dubnubdubnub/Giris/hw/TMR2615F_osu_pad/ground_audit_report.md

# Ground audit: TMR2615F_osu_pad

Generated by ground_audit.py. All coordinates in mm.

## Key footprint positions

- **NT1** (NetTie_2): (116.95, 99.40)
- **U7** (AT32F405RBT7-7): (99.00, 107.50)
- **U13** (TMR2615x): (110.00, 121.00)
- Distance NT1 -> U7: 19.69 mm
- Distance NT1 -> U13: 22.69 mm

## Inner-layer routed copper (non-ground)

If these are large, the inner layer can't be treated as a continuous plane.

- **In1.Cu**: 0.0 mm of non-GND/GNDA track
- **In2.Cu**: 211.3 mm of non-GND/GNDA track

## Tracks per layer per net (totals in mm)

| Layer | Net | Total length (mm) |
|---|---|---:|
| F.Cu | GNDA | 100.9 |
| F.Cu | +3.3VA | 43.6 |
| F.Cu | /Key2/DOUT | 40.0 |
| F.Cu | /OTGHS1_D+ | 31.7 |
| F.Cu | /OTGHS1_D- | 31.7 |
| F.Cu | +5V | 29.0 |
| F.Cu | /OTGFS1_D- | 27.1 |
| F.Cu | /OTGFS1_D+ | 26.9 |
| F.Cu | GND | 25.8 |
| F.Cu | +3.3V | 19.9 |
| F.Cu | /I2C2_SDA | 15.5 |
| F.Cu | /SPI3_CS | 15.5 |
| F.Cu | /Key4/DOUT | 14.3 |
| F.Cu | /Key3/DOUT | 14.3 |
| F.Cu | /Key/DOUT | 14.3 |
| F.Cu | /I2C2_SCL | 13.7 |
| F.Cu | /DIN | 12.7 |
| F.Cu | Net-(U19-VOUT) | 12.1 |
| F.Cu | Net-(U13-VOUT) | 12.1 |
| F.Cu | Net-(U16-VOUT) | 12.0 |
| F.Cu | Net-(U25-VOUT) | 12.0 |
| F.Cu | Net-(U22-VOUT) | 12.0 |
| F.Cu | Net-(U10-VOUT) | 12.0 |
| F.Cu | /TMUX_SEL | 11.7 |
| F.Cu | /USART1_RX | 9.2 |
| F.Cu | /SYS_SWDIO | 8.5 |
| F.Cu | /Key1/DOUT | 6.9 |
| F.Cu | Net-(J1-DN1) | 5.6 |
| F.Cu | Net-(U7-VDDA) | 5.1 |
| F.Cu | /ADC1_IN3 | 4.8 |
| F.Cu | /RCC_OSC_IN | 4.7 |
| F.Cu | /ADC1_IN0 | 4.2 |
| F.Cu | Net-(U7-PC7) | 4.2 |
| F.Cu | Net-(U7-PC6) | 4.2 |
| F.Cu | Net-(J1-DP1) | 4.0 |
| F.Cu | /TMUX_S2B | 3.4 |
| F.Cu | /SWO | 3.2 |
| F.Cu | /ADC1_IN1 | 3.1 |
| F.Cu | Net-(U5-ILIM) | 3.1 |
| F.Cu | /USART1_TX | 3.0 |
| F.Cu | /TMUX_S1B | 2.9 |
| F.Cu | /SPI3_MOSI | 2.8 |
| F.Cu | /TMUX_S2A | 2.7 |
| F.Cu | /ADC1_IN2 | 2.6 |
| F.Cu | /RCC_OSC_OUT | 2.6 |
| F.Cu | /TMUX_S3B | 2.6 |
| F.Cu | /TMUX_S3A | 2.5 |
| F.Cu | /TMUX_S1A | 2.5 |
| F.Cu | /SPI3_MISO | 2.3 |
| F.Cu | /SPI3_SCK | 2.3 |
| F.Cu | /IO1 | 2.2 |
| F.Cu | /USART1_CK | 1.7 |
| F.Cu | Net-(U1-VDDB) | 1.6 |
| F.Cu | Net-(U1-VDDA) | 1.6 |
| F.Cu | Net-(LED1-K) | 1.6 |
| F.Cu | Net-(U5-FAULT#) | 1.3 |
| F.Cu | Net-(J2-CC1) | 1.3 |
| F.Cu | Net-(J4-CC1) | 1.3 |
| F.Cu | /UART8_RX | 1.3 |
| F.Cu | Net-(J2-CC2) | 1.3 |
| F.Cu | Net-(J4-CC2) | 1.2 |
| F.Cu | Net-(U9-NR) | 1.2 |
| F.Cu | /SYS_SWCLK | 1.0 |
| F.Cu | /UART8_TX | 1.0 |
| F.Cu | /TMUX_S4A | 0.9 |
| F.Cu | /TMUX_S4B | 0.8 |
| F.Cu | /UART7_TX | 0.8 |
| B.Cu | +3.3VA | 112.7 |
| B.Cu | /TMUX_S2B | 48.4 |
| B.Cu | /TMUX_S1A | 47.9 |
| B.Cu | /TMUX_S3B | 47.4 |
| B.Cu | /TMUX_S3A | 36.7 |
| B.Cu | /TMUX_S2A | 30.3 |
| B.Cu | /IO1 | 24.3 |
| B.Cu | +3.3V | 23.6 |
| B.Cu | /TMUX_S1B | 20.1 |
| B.Cu | /SPI3_MOSI | 19.0 |
| B.Cu | /SPI3_MISO | 17.0 |
| B.Cu | /USART1_CK | 16.6 |
| B.Cu | /Key2/DOUT | 15.5 |
| B.Cu | /SPI3_SCK | 14.7 |
| B.Cu | /UART8_TX | 14.7 |
| B.Cu | /USART1_TX | 13.3 |
| B.Cu | /UART8_RX | 12.6 |
| B.Cu | /SWO | 12.2 |
| B.Cu | /DIN | 8.1 |
| B.Cu | /SYS_SWCLK | 7.6 |
| B.Cu | /Key1/DOUT | 7.3 |
| B.Cu | /USART1_RX | 5.2 |
| B.Cu | /OTGFS1_D+ | 1.2 |
| B.Cu | /OTGHS1_D+ | 1.1 |
| B.Cu | Net-(J1-DP1) | 1.1 |
| B.Cu | GND | 1.0 |
| B.Cu | /SYS_SWDIO | 0.9 |
| In1.Cu | GNDA | 21.3 |
| In2.Cu | +5V | 193.9 |
| In2.Cu | +3.3V | 17.4 |

## Ground stitching vias

| Net | Top layer | Bottom layer | Count |
|---|---|---|---:|
| GND | F.Cu | B.Cu | 40 |
| GNDA | F.Cu | B.Cu | 46 |

## Return-path discontinuities

Each row is a sample point along a signal track where the *reference plane* net changes from one ground island to another. Return current at that point must take the long way around (typically through NT1).

| Signal net | Track layer | Ref layer | X (mm) | Y (mm) | From -> To | Detour to NT1 (mm) |
|---|---|---|---:|---:|---|---:|
| +3.3VA | F.Cu | In1.Cu | 109.98 | 137.61 | GND -> (no fill) | 38.8 |
| +3.3VA | F.Cu | In1.Cu | 113.43 | 129.71 | GND -> (no fill) | 30.5 |
| +3.3VA | F.Cu | In1.Cu | 129.03 | 118.56 | GND -> (no fill) | 22.7 |
| +3.3VA | F.Cu | In1.Cu | 90.93 | 118.56 | GND -> (no fill) | 32.3 |
| +3.3VA | F.Cu | In1.Cu | 107.79 | 130.98 | GND -> (no fill) | 32.9 |
| +3.3VA | F.Cu | In1.Cu | 117.56 | 129.71 | GND -> (no fill) | 30.3 |
| +3.3VA | F.Cu | In1.Cu | 116.01 | 129.71 | GND -> (no fill) | 30.3 |
| +3.3VA | F.Cu | In1.Cu | 114.47 | 129.71 | GND -> (no fill) | 30.4 |
| +3.3VA | F.Cu | In1.Cu | 96.98 | 129.37 | GND -> (no fill) | 36.0 |
| +3.3VA | F.Cu | In1.Cu | 109.98 | 118.56 | GND -> (no fill) | 20.4 |
| +3.3VA | F.Cu | In1.Cu | 90.93 | 137.61 | GND -> (no fill) | 46.2 |
| +3.3VA | F.Cu | In1.Cu | 129.03 | 137.61 | GND -> (no fill) | 40.1 |
| +3.3VA | F.Cu | In1.Cu | 103.97 | 130.98 | GND -> (no fill) | 34.1 |
| +3.3VA | B.Cu | In2.Cu | 108.59 | 131.19 | GNDA -> (no fill) | 32.9 |
| +3.3VA | B.Cu | In2.Cu | 102.04 | 131.34 | GNDA -> (no fill) | 35.3 |
| +3.3VA | B.Cu | In2.Cu | 122.42 | 129.76 | GNDA -> (no fill) | 30.8 |
| +3.3VA | B.Cu | In2.Cu | 119.14 | 129.76 | GNDA -> (no fill) | 30.4 |
| +3.3VA | B.Cu | In2.Cu | 115.92 | 129.71 | GNDA -> (no fill) | 30.3 |
| +3.3VA | B.Cu | In2.Cu | 117.57 | 129.71 | GNDA -> (no fill) | 30.3 |
| +3.3VA | B.Cu | In2.Cu | 118.64 | 130.05 | GNDA -> (no fill) | 30.7 |
| +3.3VA | B.Cu | In2.Cu | 113.41 | 129.71 | GNDA -> (no fill) | 30.5 |
| +3.3VA | B.Cu | In2.Cu | 91.74 | 127.85 | GNDA -> (no fill) | 38.0 |
| +3.3VA | B.Cu | In2.Cu | 114.51 | 129.71 | GNDA -> (no fill) | 30.4 |
| +3.3VA | B.Cu | In2.Cu | 128.55 | 118.43 | GNDA -> (no fill) | 22.3 |
| +3.3VA | B.Cu | In2.Cu | 94.91 | 129.37 | GNDA -> (no fill) | 37.2 |
| +3.3VA | B.Cu | In2.Cu | 115.65 | 112.87 | +3.3VA -> GNDA | 13.5 |
| +5V | F.Cu | In1.Cu | 110.62 | 98.12 | GND -> (no fill) | 6.5 |
| +5V | F.Cu | In1.Cu | 95.62 | 98.38 | GND -> (no fill) | 21.4 |
| +5V | F.Cu | In1.Cu | 97.91 | 125.30 | GND -> (no fill) | 32.2 |
| +5V | F.Cu | In1.Cu | 100.50 | 98.34 | GND -> (no fill) | 16.5 |
| +5V | F.Cu | In1.Cu | 116.96 | 125.30 | GND -> (no fill) | 25.9 |
| +5V | F.Cu | In1.Cu | 97.91 | 144.35 | GND -> (no fill) | 48.8 |
| +5V | F.Cu | In1.Cu | 115.50 | 98.26 | GND -> (no fill) | 1.8 |
| +5V | F.Cu | In1.Cu | 122.30 | 132.45 | GND -> (no fill) | 33.5 |
| +5V | F.Cu | In1.Cu | 105.60 | 97.09 | GND -> (no fill) | 11.6 |
| +5V | F.Cu | In1.Cu | 136.01 | 144.35 | GND -> (no fill) | 48.8 |
| +5V | F.Cu | In1.Cu | 90.55 | 97.09 | GND -> (no fill) | 26.5 |
| +5V | F.Cu | In1.Cu | 116.96 | 144.35 | GND -> (no fill) | 45.0 |
| +5V | F.Cu | In1.Cu | 114.90 | 103.20 | GNDA -> (no fill) | 4.3 |
| +5V | F.Cu | In1.Cu | 136.01 | 125.30 | GND -> (no fill) | 32.2 |
| +5V | In2.Cu | In1.Cu | 98.20 | 125.63 | GND -> (no fill) | 32.2 |
| +5V | In2.Cu | In1.Cu | 122.68 | 132.37 | GND -> (no fill) | 33.5 |
| +5V | In2.Cu | In1.Cu | 136.30 | 125.80 | GND -> (no fill) | 32.7 |
| +5V | In2.Cu | In1.Cu | 117.76 | 144.35 | GND -> (no fill) | 45.0 |
| +5V | In2.Cu | In1.Cu | 117.61 | 125.66 | GND -> (no fill) | 26.3 |
| +5V | In2.Cu | In1.Cu | 120.67 | 103.91 | GND -> (no fill) | 5.8 |
| +5V | In2.Cu | In1.Cu | 90.18 | 97.98 | GND -> (no fill) | 26.8 |
| +3.3V | F.Cu | In1.Cu | 98.12 | 114.23 | GND -> (no fill) | 24.0 |
| +3.3V | F.Cu | In1.Cu | 88.93 | 109.94 | GND -> (no fill) | 29.9 |
| +3.3V | F.Cu | In1.Cu | 97.66 | 114.23 | GND -> (no fill) | 24.3 |
| +3.3V | F.Cu | In1.Cu | 105.65 | 102.29 | GND -> (no fill) | 11.7 |
| +3.3V | B.Cu | In2.Cu | 95.54 | 101.18 | GND -> (no fill) | 21.5 |
| +3.3V | B.Cu | In2.Cu | 95.98 | 101.62 | GND -> (no fill) | 21.1 |
| +3.3V | B.Cu | In2.Cu | 88.97 | 110.40 | GND -> (no fill) | 30.1 |
| +3.3V | B.Cu | In2.Cu | 88.77 | 98.85 | GND -> (no fill) | 28.2 |
| +3.3V | In2.Cu | In1.Cu | 97.89 | 113.94 | GND -> (no fill) | 24.0 |
| /USART1_RX | F.Cu | In1.Cu | 90.19 | 105.05 | GND -> (no fill) | 27.3 |
| /USART1_RX | F.Cu | In1.Cu | 93.15 | 103.07 | GND -> (no fill) | 24.1 |
| /USART1_RX | B.Cu | In2.Cu | 90.28 | 105.22 | GND -> (no fill) | 27.3 |
| /USART1_RX | B.Cu | In2.Cu | 90.77 | 105.05 | GND -> (no fill) | 26.8 |
| /SPI3_SCK | F.Cu | In1.Cu | 93.12 | 110.27 | GND -> (no fill) | 26.2 |
| /SPI3_SCK | B.Cu | In2.Cu | 86.25 | 118.04 | GND -> (no fill) | 35.9 |
| /SPI3_SCK | B.Cu | In2.Cu | 89.31 | 112.38 | GND -> (no fill) | 30.5 |
| /SPI3_SCK | B.Cu | In2.Cu | 87.33 | 114.36 | GNDA -> (no fill) | 33.2 |
| /SPI3_SCK | B.Cu | In2.Cu | 85.70 | 120.40 | GND -> (no fill) | 37.6 |
| /SPI3_MISO | F.Cu | In1.Cu | 93.35 | 110.63 | GND -> (no fill) | 26.1 |
| /SPI3_MISO | B.Cu | In2.Cu | 89.87 | 112.45 | GND -> (no fill) | 30.1 |
| /SPI3_MISO | B.Cu | In2.Cu | 87.33 | 114.99 | GNDA -> (no fill) | 33.5 |
| /SPI3_MISO | B.Cu | In2.Cu | 85.70 | 122.95 | GND -> (no fill) | 39.1 |
| /SPI3_MOSI | F.Cu | In1.Cu | 93.60 | 111.06 | GND -> (no fill) | 26.1 |
| /SPI3_MOSI | B.Cu | In2.Cu | 90.43 | 112.34 | GND -> (no fill) | 29.5 |
| /SPI3_MOSI | B.Cu | In2.Cu | 87.36 | 115.41 | GNDA -> (no fill) | 33.6 |
| /SPI3_MOSI | B.Cu | In2.Cu | 85.71 | 125.48 | GND -> (no fill) | 40.7 |
| /IO1 | F.Cu | In1.Cu | 93.98 | 111.19 | GND -> (no fill) | 25.8 |
| /IO1 | B.Cu | In2.Cu | 87.40 | 117.34 | GNDA -> (no fill) | 34.6 |
| /IO1 | B.Cu | In2.Cu | 85.72 | 130.55 | GND -> (no fill) | 44.1 |
| /IO1 | B.Cu | In2.Cu | 91.29 | 112.46 | GND -> GNDA | 28.8 |
| /Key2/DOUT | F.Cu | In1.Cu | 134.85 | 128.10 | GND -> (no fill) | 33.8 |
| /Key2/DOUT | F.Cu | In1.Cu | 120.03 | 131.94 | GND -> (no fill) | 32.7 |
| /Key2/DOUT | B.Cu | In2.Cu | 120.90 | 131.57 | GNDA -> (no fill) | 32.4 |
| /Key2/DOUT | B.Cu | In2.Cu | 131.83 | 131.39 | GNDA -> (no fill) | 35.3 |
| /TMUX_S2A | F.Cu | In1.Cu | 106.80 | 106.49 | GNDA -> (no fill) | 12.4 |
| /TMUX_S2A | F.Cu | In1.Cu | 127.13 | 123.56 | GND -> (no fill) | 26.2 |
| /TMUX_S2A | B.Cu | In2.Cu | 106.99 | 105.96 | GNDA -> (no fill) | 11.9 |
| /USART1_TX | F.Cu | In1.Cu | 93.72 | 103.08 | GND -> (no fill) | 23.5 |
| /USART1_TX | B.Cu | In2.Cu | 87.00 | 104.44 | GND -> (no fill) | 30.4 |
| /USART1_TX | B.Cu | In2.Cu | 85.70 | 107.70 | GND -> (no fill) | 32.3 |
| /SWO | F.Cu | In1.Cu | 95.13 | 107.70 | GND -> (no fill) | 23.3 |
| /SWO | B.Cu | In2.Cu | 94.73 | 107.74 | GND -> (no fill) | 23.7 |
| /SWO | B.Cu | In2.Cu | 87.29 | 105.76 | GND -> (no fill) | 30.3 |
| /TMUX_S2B | F.Cu | In1.Cu | 89.03 | 142.61 | GND -> (no fill) | 51.4 |
| /TMUX_S2B | F.Cu | In1.Cu | 105.36 | 106.56 | GNDA -> (no fill) | 13.6 |
| /TMUX_S2B | B.Cu | In2.Cu | 88.29 | 142.39 | GNDA -> (no fill) | 51.7 |
| /TMUX_S3B | F.Cu | In1.Cu | 105.58 | 108.52 | GNDA -> (no fill) | 14.6 |
| /TMUX_S3B | F.Cu | In1.Cu | 127.13 | 142.61 | GND -> (no fill) | 44.4 |
| /TMUX_S3B | B.Cu | In2.Cu | 126.24 | 142.24 | GNDA -> (no fill) | 43.8 |
| /UART8_TX | F.Cu | In1.Cu | 97.05 | 104.70 | GND -> (no fill) | 20.6 |
| /UART8_TX | B.Cu | In2.Cu | 88.44 | 100.26 | GND -> (no fill) | 28.5 |
| /UART8_TX | B.Cu | In2.Cu | 86.06 | 100.26 | GND -> (no fill) | 30.9 |
| /USART1_CK | F.Cu | In1.Cu | 94.93 | 103.70 | GND -> (no fill) | 22.4 |
| /USART1_CK | B.Cu | In2.Cu | 94.92 | 103.70 | GND -> (no fill) | 22.4 |
| /USART1_CK | B.Cu | In2.Cu | 86.39 | 109.86 | GND -> (no fill) | 32.3 |
| /OTGFS1_D+ | F.Cu | In1.Cu | 97.35 | 98.06 | GND -> (no fill) | 19.6 |
| /OTGFS1_D+ | F.Cu | In1.Cu | 94.05 | 93.82 | GND -> (no fill) | 23.6 |
| /OTGFS1_D+ | F.Cu | In1.Cu | 98.35 | 98.07 | GND -> (no fill) | 18.6 |
| /TMUX_S1A | F.Cu | In1.Cu | 89.03 | 123.56 | GND -> (no fill) | 36.9 |
| /TMUX_S1A | B.Cu | In2.Cu | 88.50 | 128.48 | GNDA -> (no fill) | 40.7 |
| /TMUX_S1A | B.Cu | In2.Cu | 88.50 | 124.07 | GNDA -> (no fill) | 37.7 |
| /Key1/DOUT | F.Cu | In1.Cu | 127.44 | 125.30 | GND -> (no fill) | 27.9 |
| /Key1/DOUT | F.Cu | In1.Cu | 119.77 | 126.53 | GND -> (no fill) | 27.3 |
| /Key1/DOUT | B.Cu | In2.Cu | 126.73 | 125.50 | GNDA -> (no fill) | 27.9 |
| Net-(U13-VOUT) | F.Cu | In1.Cu | 106.86 | 116.10 | GND -> (no fill) | 19.5 |
| Net-(U13-VOUT) | F.Cu | In1.Cu | 107.57 | 115.87 | GND -> (no fill) | 19.0 |
| Net-(U16-VOUT) | F.Cu | In1.Cu | 125.69 | 116.24 | GND -> (no fill) | 19.0 |
| Net-(U16-VOUT) | F.Cu | In1.Cu | 126.62 | 115.87 | GND -> (no fill) | 19.1 |
| /SYS_SWDIO | F.Cu | In1.Cu | 88.05 | 102.29 | GND -> (no fill) | 29.0 |
| /SYS_SWDIO | B.Cu | In2.Cu | 87.99 | 102.29 | GND -> (no fill) | 29.1 |
| Net-(U19-VOUT) | F.Cu | In1.Cu | 88.24 | 134.92 | GND -> (no fill) | 45.7 |
| Net-(U19-VOUT) | F.Cu | In1.Cu | 87.61 | 135.13 | GND -> (no fill) | 46.2 |
| Net-(U25-VOUT) | F.Cu | In1.Cu | 125.69 | 135.29 | GND -> (no fill) | 36.9 |
| Net-(U25-VOUT) | F.Cu | In1.Cu | 126.62 | 134.92 | GND -> (no fill) | 36.8 |
| Net-(J1-DP1) | F.Cu | In1.Cu | 128.35 | 96.84 | GND -> (no fill) | 11.7 |
| Net-(J1-DP1) | B.Cu | In2.Cu | 128.05 | 96.50 | GND -> (no fill) | 11.5 |
| /UART8_RX | F.Cu | In1.Cu | 95.45 | 103.67 | GND -> (no fill) | 21.9 |
| /UART8_RX | B.Cu | In2.Cu | 87.31 | 101.69 | GND -> (no fill) | 29.7 |
| /DIN | F.Cu | In1.Cu | 96.92 | 124.18 | GND -> (no fill) | 31.9 |
| /DIN | B.Cu | In2.Cu | 95.28 | 117.22 | GNDA -> (no fill) | 28.1 |
| Net-(U10-VOUT) | F.Cu | In1.Cu | 88.52 | 115.87 | GND -> (no fill) | 32.9 |
| Net-(U10-VOUT) | F.Cu | In1.Cu | 87.59 | 116.24 | GND -> (no fill) | 33.9 |
| Net-(U22-VOUT) | F.Cu | In1.Cu | 106.64 | 135.29 | GND -> (no fill) | 37.3 |
| Net-(U22-VOUT) | F.Cu | In1.Cu | 107.57 | 134.92 | GND -> (no fill) | 36.7 |
| /SYS_SWCLK | F.Cu | In1.Cu | 93.38 | 107.90 | GND -> (no fill) | 25.1 |
| /UART7_TX | F.Cu | In1.Cu | 94.68 | 102.01 | GND -> (no fill) | 22.4 |
| /ADC1_IN0 | F.Cu | In1.Cu | 103.68 | 109.07 | GND -> (no fill) | 16.4 |
| /ADC1_IN1 | F.Cu | In1.Cu | 103.95 | 108.77 | GNDA -> (no fill) | 16.0 |
| /ADC1_IN2 | F.Cu | In1.Cu | 104.59 | 107.06 | GND -> GNDA | 14.5 |
| /ADC1_IN3 | F.Cu | In1.Cu | 105.38 | 105.65 | GND -> (no fill) | 13.2 |
| /TMUX_SEL | F.Cu | In1.Cu | 105.93 | 105.20 | GNDA -> (no fill) | 12.5 |
| /I2C2_SCL | F.Cu | In1.Cu | 85.70 | 112.78 | GND -> (no fill) | 34.0 |
| /I2C2_SDA | F.Cu | In1.Cu | 85.77 | 115.25 | GND -> (no fill) | 35.0 |
| /TMUX_S3A | F.Cu | In1.Cu | 108.08 | 142.61 | GND -> (no fill) | 44.1 |
| /TMUX_S4B | F.Cu | In1.Cu | 107.20 | 109.20 | GNDA -> (no fill) | 13.8 |
| /TMUX_S4A | F.Cu | In1.Cu | 107.60 | 109.15 | GNDA -> (no fill) | 13.5 |
| /TMUX_S1B | F.Cu | In1.Cu | 108.08 | 123.56 | GND -> (no fill) | 25.7 |
| Net-(U7-VDDA) | F.Cu | In1.Cu | 103.37 | 109.33 | GND -> (no fill) | 16.8 |

## Interpretation hints

- A crossing with `from`/`to` between **GND** and **GNDA**: real return-path discontinuity. Return current must reach NT1 (single bond point) to close the loop. Loop area ~= 2 * detour_to_NT1 * (dielectric thickness to ref layer). For F.Cu -> In1.Cu that's ~0.21 mm; loop area = detour_mm * 0.42 mm^2.
- A crossing involving **(no fill)**: the reference layer has a copper void below the trace. Either a routed track on the plane layer or an unfilled gap. These are worse than GND<->GNDA transitions because there's no nearby return at all.
- Many crossings on **In1.Cu** as ref layer means the digital top-side routing is the main beneficiary/victim of the split. If the count is high, the split is actively hurting signal integrity, not helping.
- Zero crossings means the split exists but no signal actually crosses it -- the split is harmless but also pointless.
