dubnubdubnub/Giris/hw/giris/output/giris.pdf

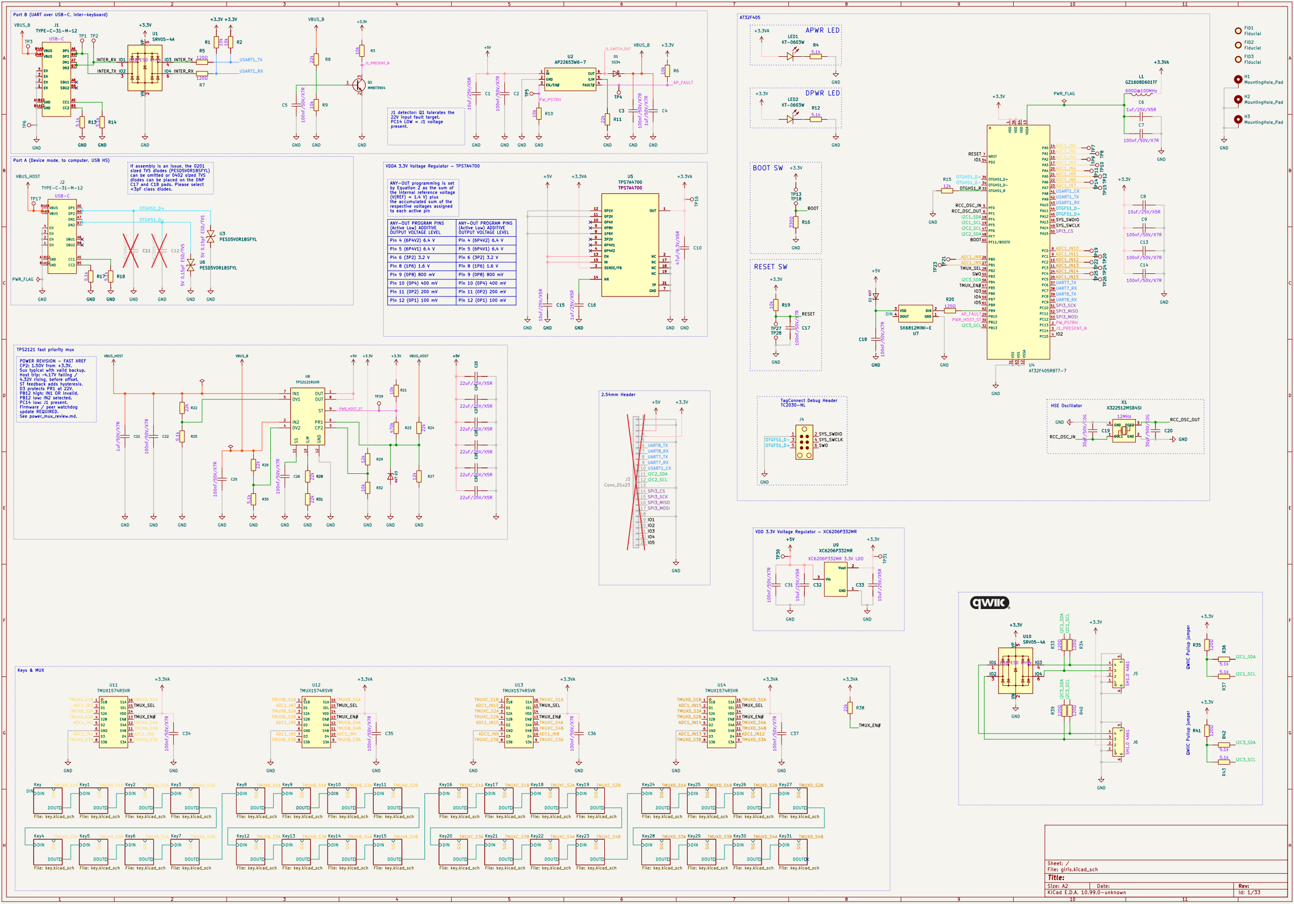
[picture p2: figure]
FGH; FGH Date:; KiCad E.D.A. 10.99.0-unknown; Size: A2; Rev:; Title:; File: giris.kicad_sch; Sheet: /; DIN; DOUTSIG; Key2; File: key.kicad_sch; Key3; Key8; Key9; Key10; File: key.kicad_sch DIN; Key4; Key5; Key6; Key12; Key14; Key15; Key7; Key11; Key File: key.kicad_sch; Key13; Key1; Key16; Key20; Key17; Key18; Key22; Key21; Key19; Key23; Key24; Key28; Key25; Key29; Key26; Key30; Key27; Key31; VBUS_HOST; GND; J4 ³³⁰Ω; R16 +5V ¹⁰k; +3.3V GND; R21 GND; H3MountingHole_Pad D2 4V7; LED1 KT-0603W; Q1MMBT3904; FID1; Fiducial; XC6206P332MR 3.3V LDO; Vout; Vin 3; H2MountingHole_Pad H1MountingHole_Pad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

C31 ²²k R28 100nF/50V/X7R C5 ¹⁰k R1 | FID2
5.1kR36120Ω R34 R33 120Ω ²²k R31 | 12k | R27 | GND ⁴⁷⁰k | R23 30pF/50V/C0G | C12 | 10uF/25V/X5R
(Active Low) ADDITIVE OUTPUT VOLTAGE LEVEL | ANY-OUT PROGRAM PINS
(Active Low) ADDITIVE OUTPUT VOLTAGE LEVEL Pin 4 (6P4V2) 6.4 V | Pin 4 (6P4V2) 6.4 V Pin 5 (6P4V1) 6.4 V | Pin 5 (6P4V1) 6.4 V Pin 6 (3P2) 3.2 V | Pin 6 (3P2) 3.2 V Pin 8 (1P6) 1.6 V | Pin 8 (1P6) 1.6 V Pin 9 (0P8) 800 mV | Pin 9 (0P8) 800 mV Pin 10 (0P4) 400 mV | Pin 10 (0P4) 400 mV Pin 11 (0P2) 200 mV | Pin 11 (0P2) 200 mV Pin 12 (0P1) 100 mV | Pin 12 (0P1) 100 mV | 2.54mm Header

Port A (Device mode, to computer, USB HS) Port B (UART over USB-C, inter-keyboard)

sized TVS diodes (PESD5V0R1BSFYL) can be omitted or 0402 sized TVS

C17 and C18 pads. Please select <3pF class diodes. | VDDA 3.3V Voltage Regulator — TPS7A4700

ANY-OUT programming is set by Equation 2 as the sum of

J1 detector: Q1 tolerates the 22V input fault target. PC14 LOW = J1 voltage

VDD 3.3V Voltage Regulator — XC6206P332MR

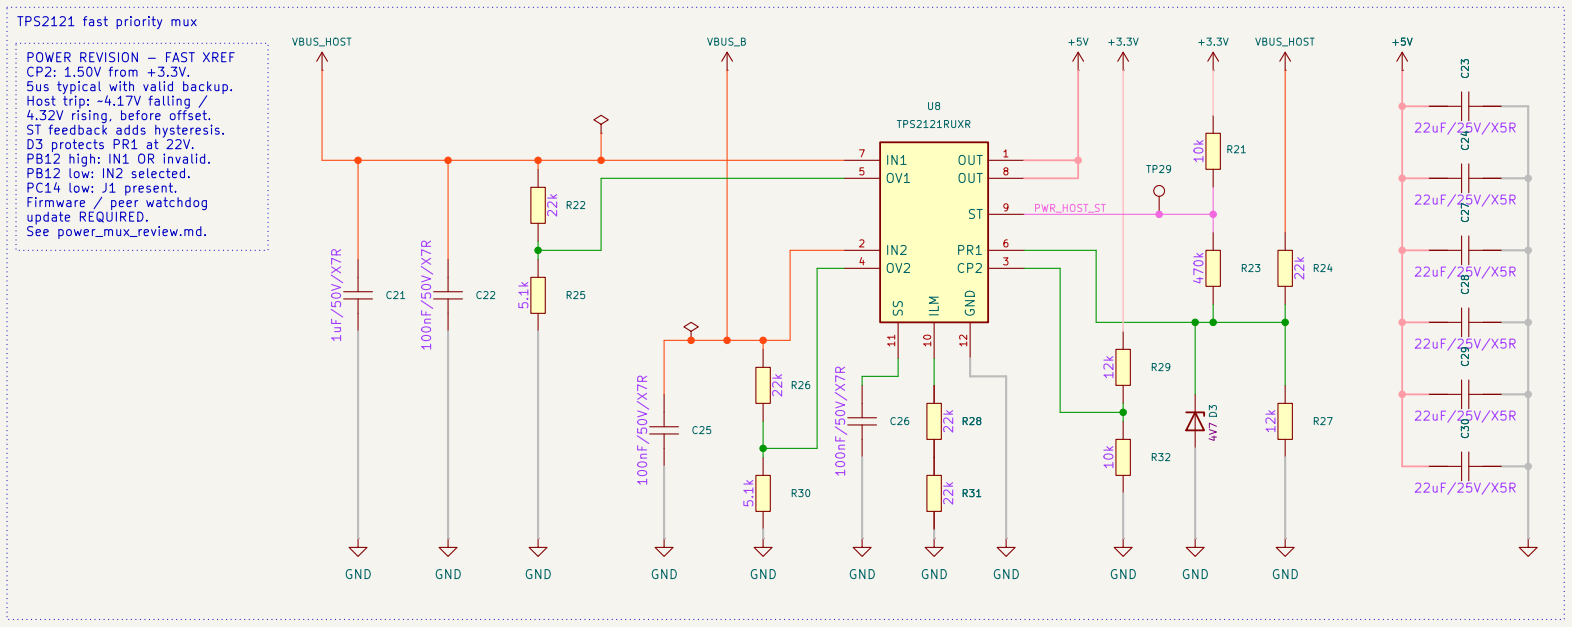
[picture p3: figure]

POWER REVISION - FAST XREF CP2: 1.50V from +3.3V. 5us typical with valid backup. Host trip: ~4.17V falling /

4.32V rising, before offset. ST feedback adds hysteresis. D3 protects PR1 at 22V. PB12 high: IN1 OR invalid. PB12 low: IN2 selected. PC14 low: J1 present. Firmware / peer watchdog

TagConnect Debug Header TC2030-NL | QWIIC Pullup jumper QWIIC Pullup jumper HSE Oscillator U3PESD5V0R1BSFYL | TP12 | +3.3VA

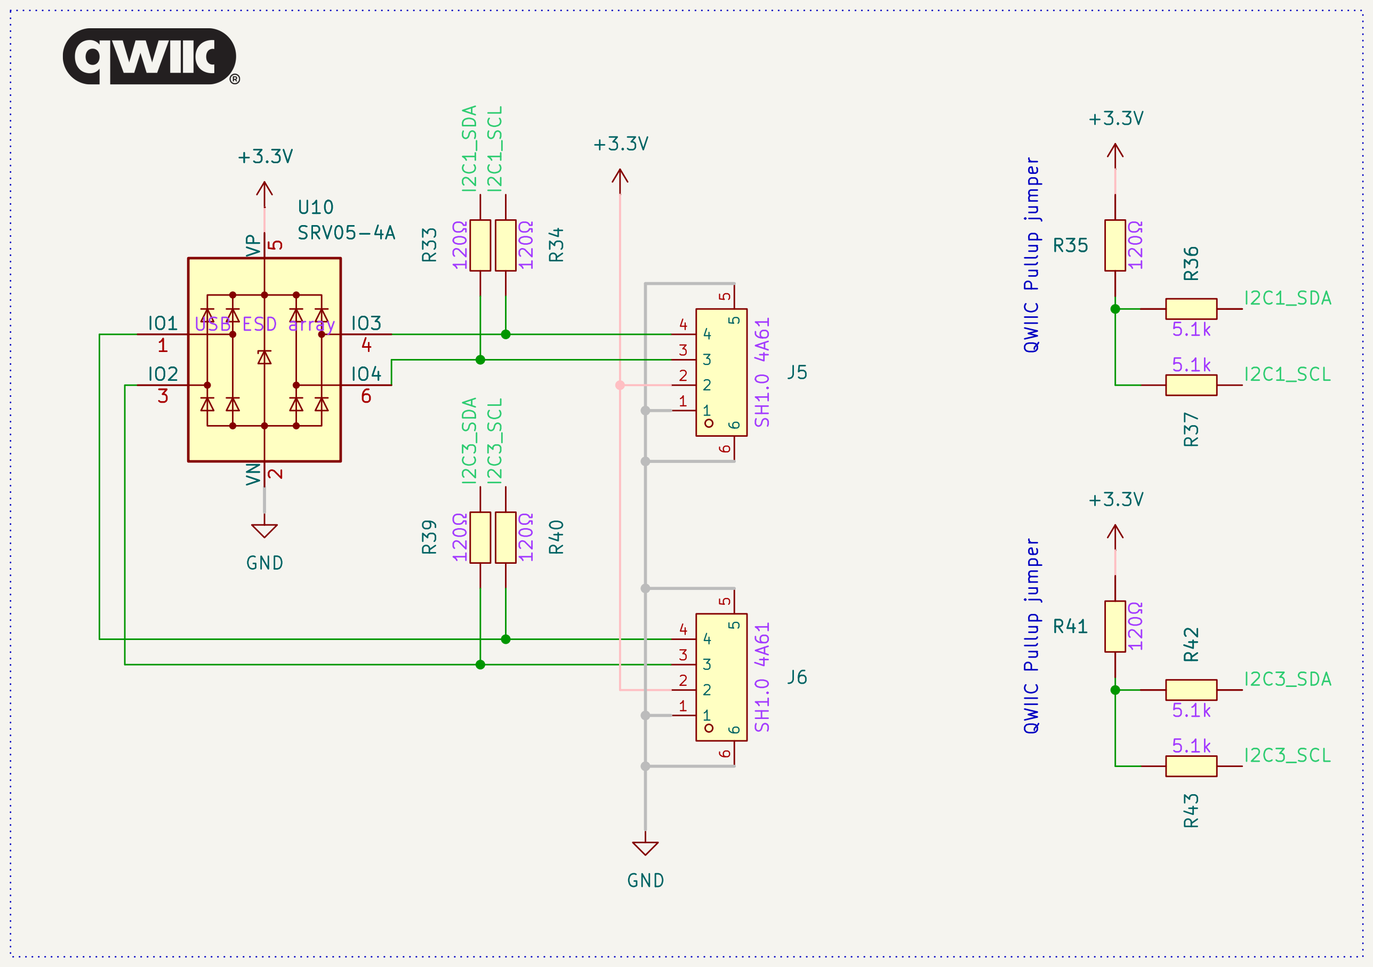
[picture p4: figure]
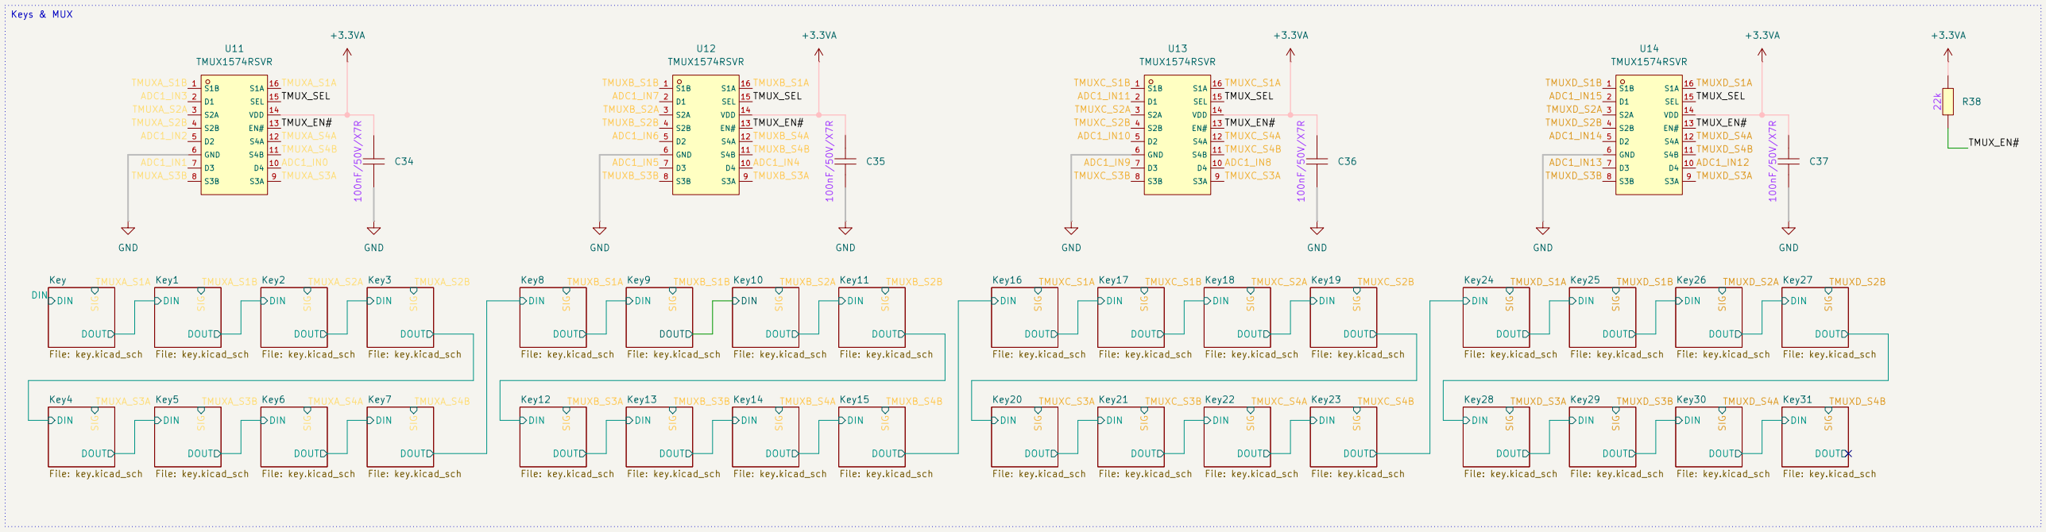
[picture p5: figure]

key.kicad_sch is used 32 times; only /Key/ is drawn here.

# The other instances (Key1, Key2, ..., Key30, Key31) are the same circuit

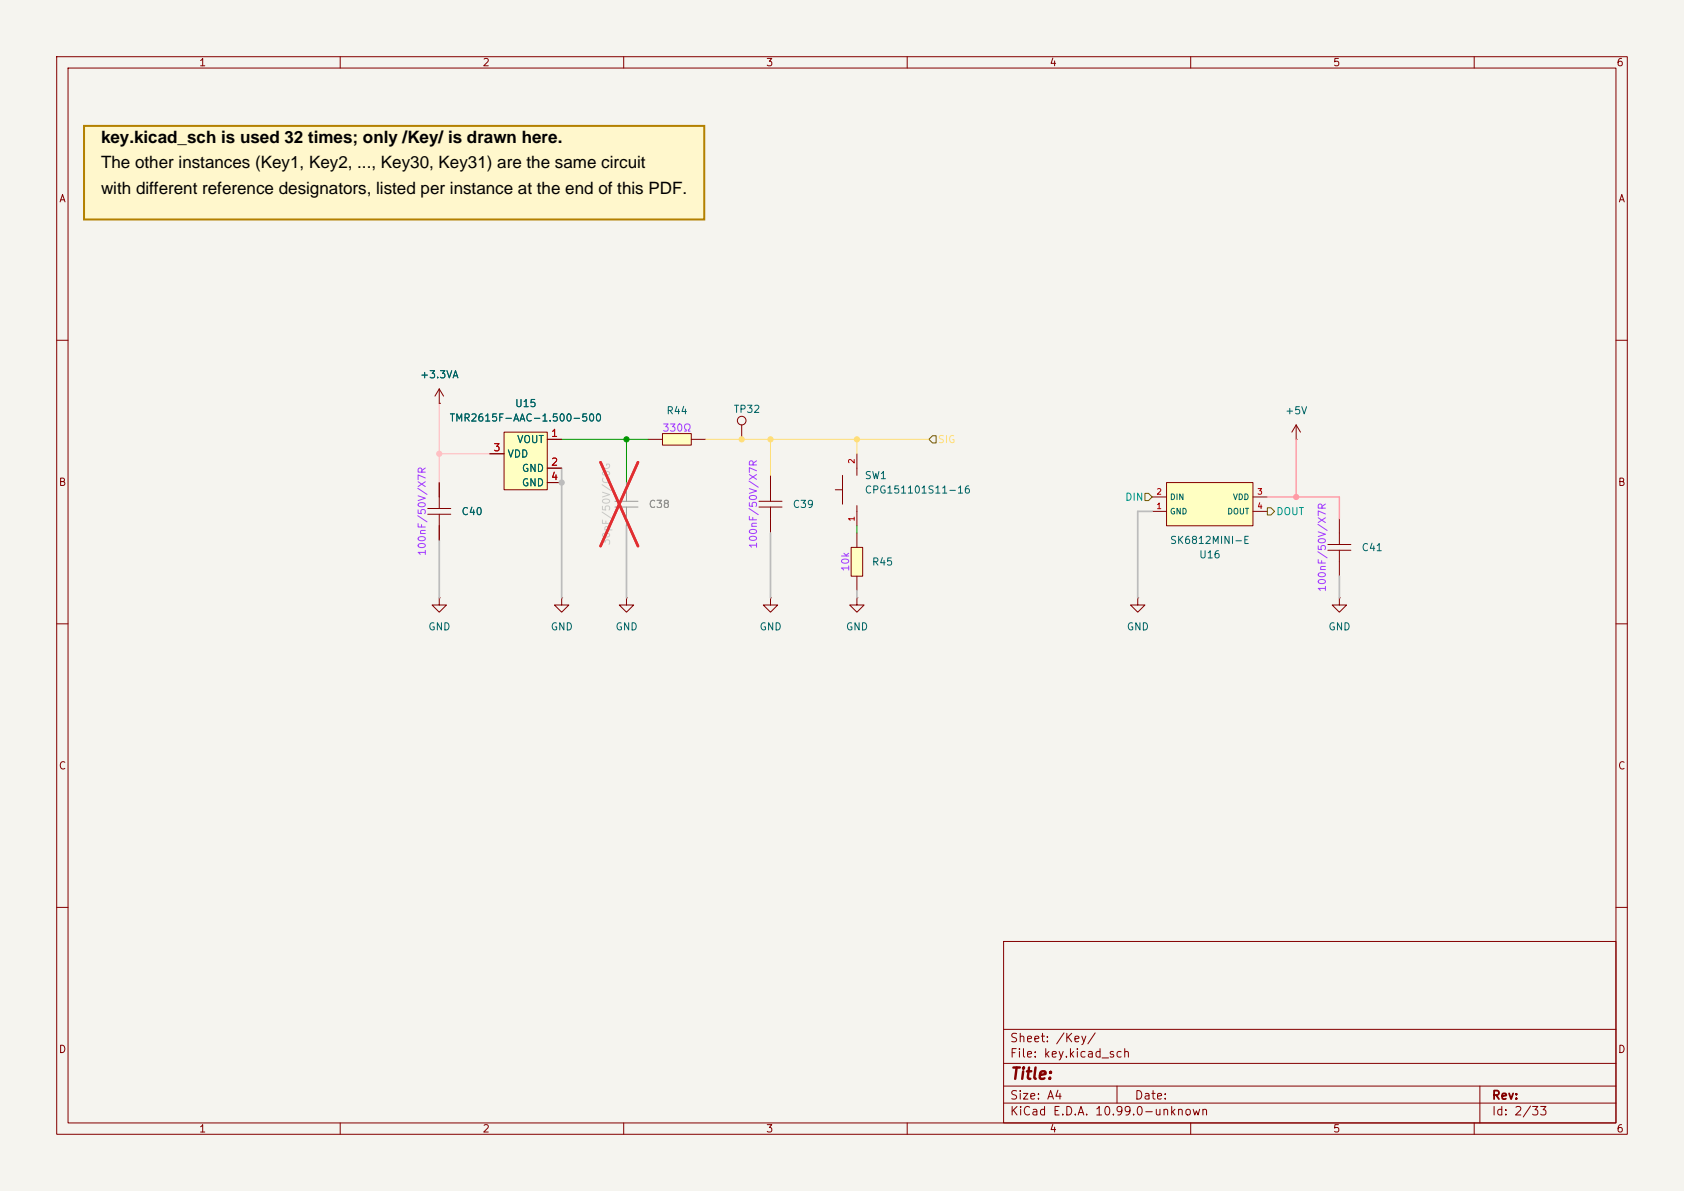
[picture p6: page 2]

with different reference designators, listed per instance at the end of this PDF.

# key.kicad_sch: reference designators per instance

This sheet is placed 32 times. The PDF draws only /Key/ (highlighted row); every other instance has the same circuit with the designators in its row. Columns follow the drawn instance's designators.

Sheet | C38 | C39 | C40 | C41 | R44 | R45 | SW1 | TP32 | U15 | U16
Key | C38 | C39 | C40 | C41 | R44 | R45 | SW1 | TP32 | U15 | U16
Key1 | C42 | C43 | C44 | C45 | R46 | R47 | SW2 | TP33 | U17 | U18
Key2 | C46 | C47 | C48 | C49 | R48 | R49 | SW3 | TP34 | U19 | U20
Key3 | C50 | C51 | C52 | C53 | R50 | R51 | SW4 | TP35 | U21 | U22
Key4 | C54 | C55 | C56 | C57 | R52 | R53 | SW5 | TP36 | U23 | U24
Key5 | C58 | C59 | C60 | C61 | R54 | R55 | SW6 | TP37 | U25 | U26
Key6 | C62 | C63 | C64 | C65 | R56 | R57 | SW7 | TP38 | U27 | U28
Key7 | C66 | C67 | C68 | C69 | R58 | R59 | SW8 | TP39 | U29 | U30
Key8 | C70 | C71 | C72 | C73 | R60 | R61 | SW9 | TP40 | U31 | U32
Key9 | C74 | C75 | C76 | C77 | R62 | R63 | SW10 | TP41 | U33 | U34
Key10 | C78 | C79 | C80 | C81 | R64 | R65 | SW11 | TP42 | U35 | U36
Key11 | C82 | C83 | C84 | C85 | R66 | R67 | SW12 | TP43 | U37 | U38
Key12 | C86 | C87 | C88 | C89 | R68 | R69 | SW13 | TP44 | U39 | U40
Key13 | C90 | C91 | C92 | C93 | R70 | R71 | SW14 | TP45 | U41 | U42
Key14 | C94 | C95 | C96 | C97 | R72 | R73 | SW15 | TP46 | U43 | U44
Key15 | C98 | C99 | C100 | C101 | R74 | R75 | SW16 | TP47 | U45 | U46
Key16 | C102 | C103 | C104 | C105 | R76 | R77 | SW17 | TP48 | U47 | U48
Key17 | C106 | C107 | C108 | C109 | R78 | R79 | SW18 | TP49 | U49 | U50
Key18 | C110 | C111 | C112 | C113 | R80 | R81 | SW19 | TP50 | U51 | U52
Key19 | C114 | C115 | C116 | C117 | R82 | R83 | SW20 | TP51 | U53 | U54
Key20 | C118 | C119 | C120 | C121 | R84 | R85 | SW21 | TP52 | U55 | U56
Key21 | C122 | C123 | C124 | C125 | R86 | R87 | SW22 | TP53 | U57 | U58
Key22 | C126 | C127 | C128 | C129 | R88 | R89 | SW23 | TP54 | U59 | U60
Key23 | C130 | C131 | C132 | C133 | R90 | R91 | SW24 | TP55 | U61 | U62
Key24 | C134 | C135 | C136 | C137 | R92 | R93 | SW25 | TP56 | U63 | U64
Key25 | C138 | C139 | C140 | C141 | R94 | R95 | SW26 | TP57 | U65 | U66
Key26 | C142 | C143 | C144 | C145 | R96 | R97 | SW27 | TP58 | U67 | U68
Key27 | C146 | C147 | C148 | C149 | R98 | R99 | SW28 | TP59 | U69 | U70
Key28 | C150 | C151 | C152 | C153 | R100 | R101 | SW29 | TP60 | U71 | U72
Key29 | C154 | C155 | C156 | C157 | R102 | R103 | SW30 | TP61 | U73 | U74
Key30 | C158 | C159 | C160 | C161 | R104 | R105 | SW31 | TP62 | U75 | U76

Sheet | C38 | C39 | C40 | C41 | R44 | R45 | SW1 | TP32 | U15 | U16
Key31 | C162 | C163 | C164 | C165 | R106 | R107 | SW32 | TP63 | U77 | U78
