dubnubdubnub/Giris/hw/TMR2615F_osu_pad/output/TMR2615F_osu_pad.pdf

# GND 30pF/50V/C0G C15 GND

6 U5

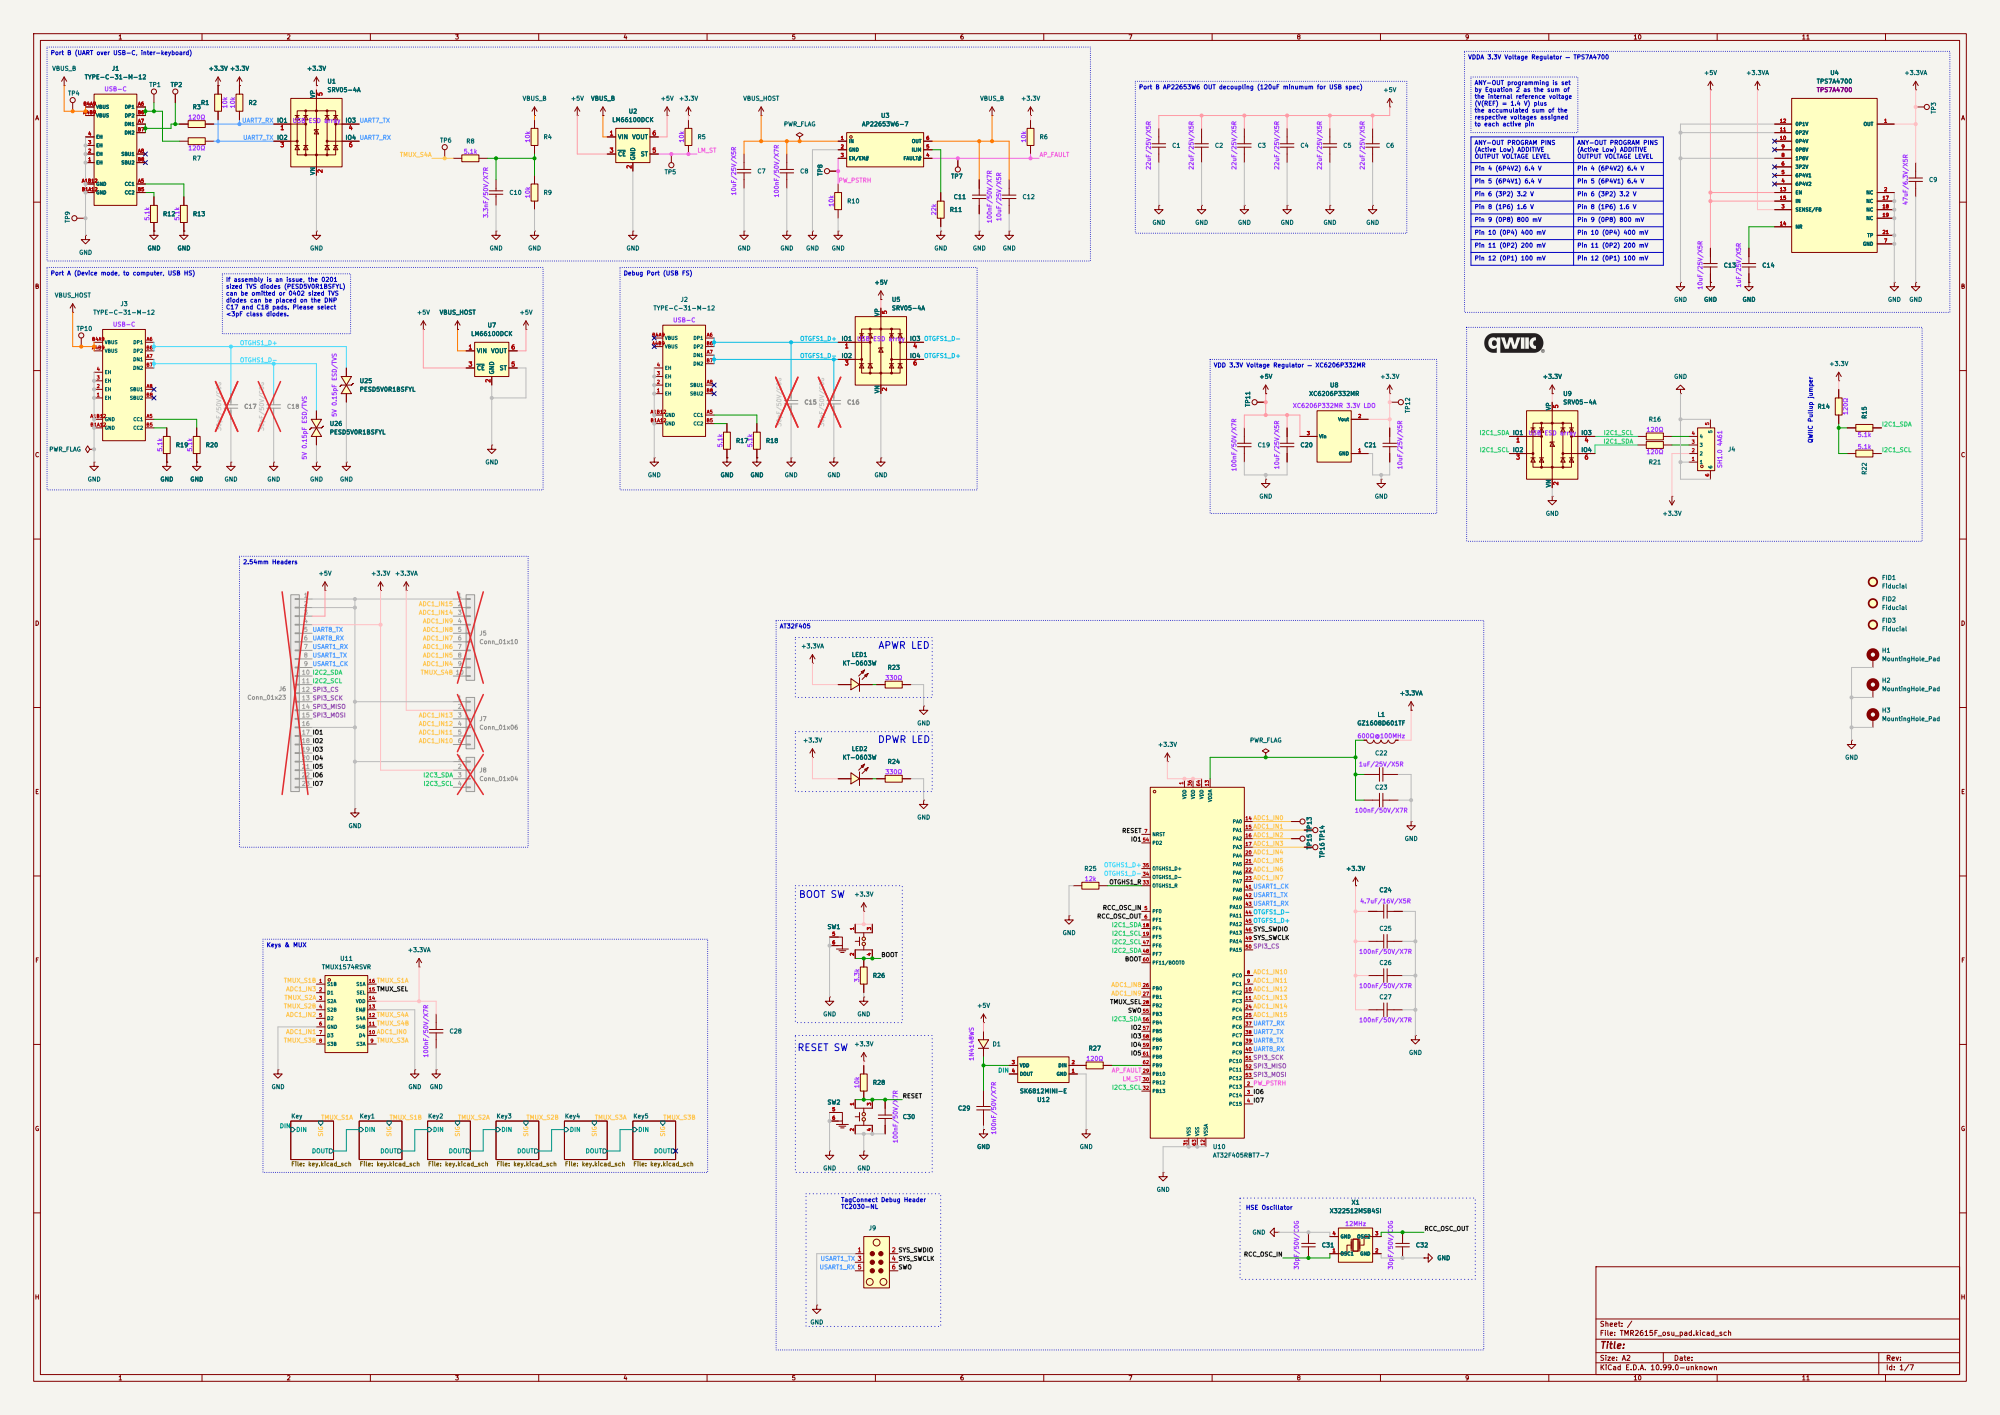
[picture p11: page 1]

Port B (UART over USB-C, inter-keyboard)
SBU2 B8 J1
TP2GND

the internal reference voltage
(V(REF) = 1.4 V) plus
the accumulated sum of the
respective voltages assigned
to each active pin

ANY-OUT PROGRAM PINS

If assembly is an issue, the 0201
sized TVS diodes (PESD5V0R1BSFYL) can be omitted or 0402 sized TVS

diodes can be placed on the DNP

HSE Oscillator RESET SW

key.kicad_sch is used 6 times; only /Key/ is drawn here.

# The other instances (Key1, Key2, Key3, Key4, Key5) are the same circuit

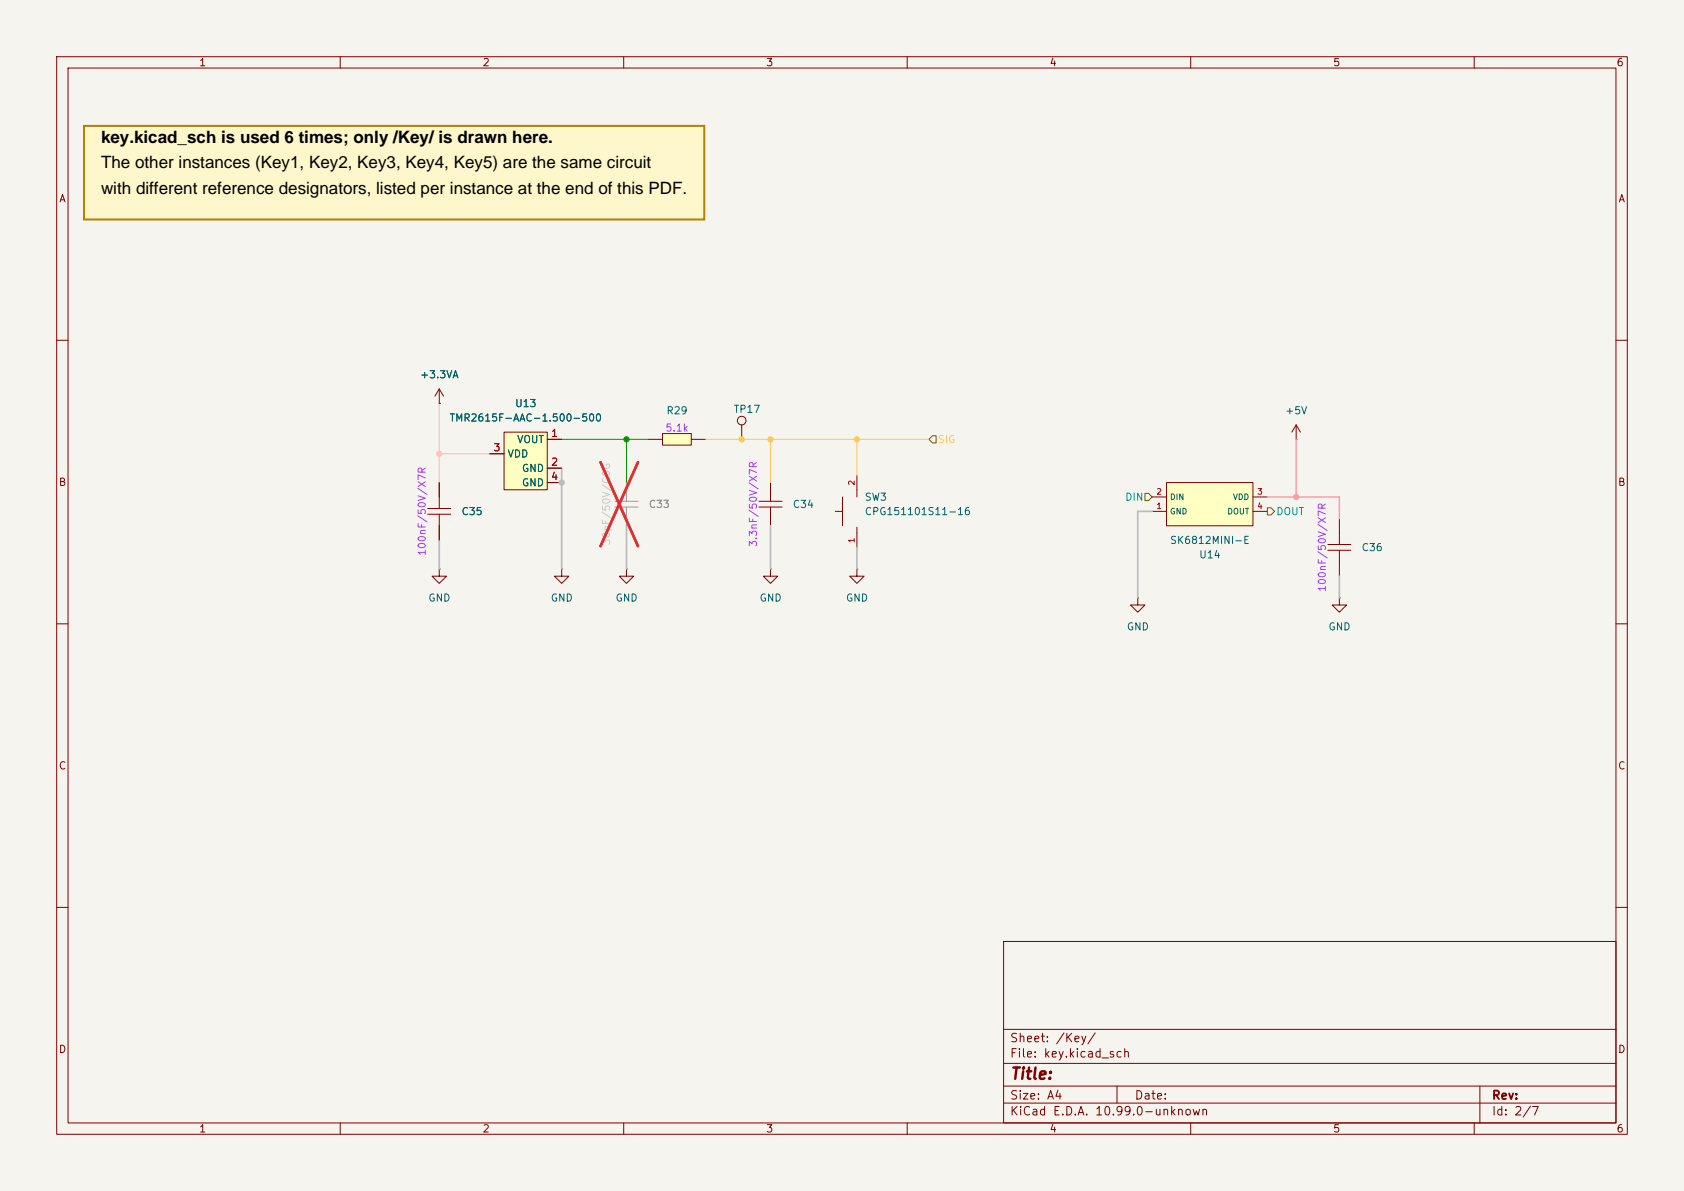
[picture p12: page 2]

with different reference designators, listed per instance at the end of this PDF.

# key.kicad_sch: reference designators per instance

This sheet is placed 6 times. The PDF draws only /Key/ (highlighted row); every other instance has the same circuit with the designators in its row. Columns follow the drawn instance's designators.

Sheet | C33 | C34 | C35 | C36 | R29 | SW3 | TP17 | U13 | U14
Key | C33 | C34 | C35 | C36 | R29 | SW3 | TP17 | U13 | U14
Key1 | C37 | C38 | C39 | C40 | R30 | SW4 | TP18 | U15 | U16
Key2 | C41 | C42 | C43 | C44 | R31 | SW5 | TP19 | U17 | U18
Key3 | C45 | C46 | C47 | C48 | R32 | SW6 | TP20 | U19 | U20
Key4 | C49 | C50 | C51 | C52 | R33 | SW7 | TP21 | U21 | U22
Key5 | C53 | C54 | C55 | C56 | R34 | SW8 | TP22 | U23 | U24
