dubnubdubnub/Giris/hw/TMR2615F_osu_pad/output/TMR2615F_osu_pad-layers.pdf

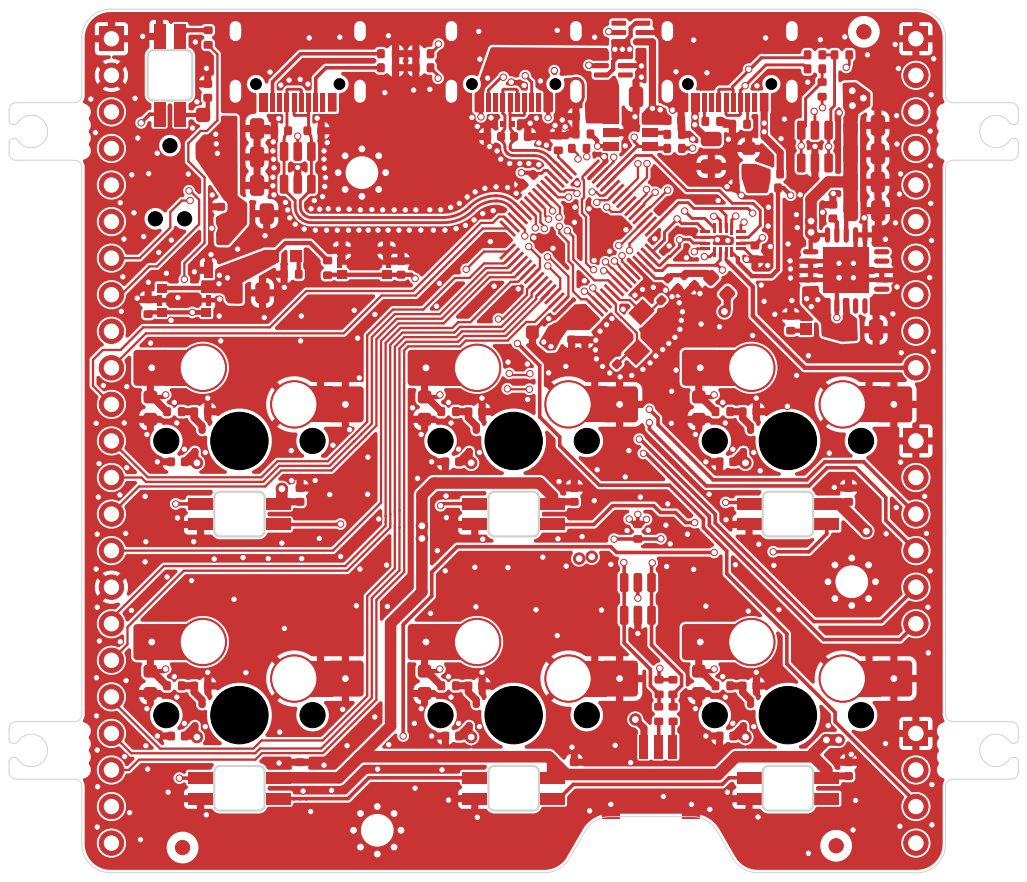
[picture p13: page 1]

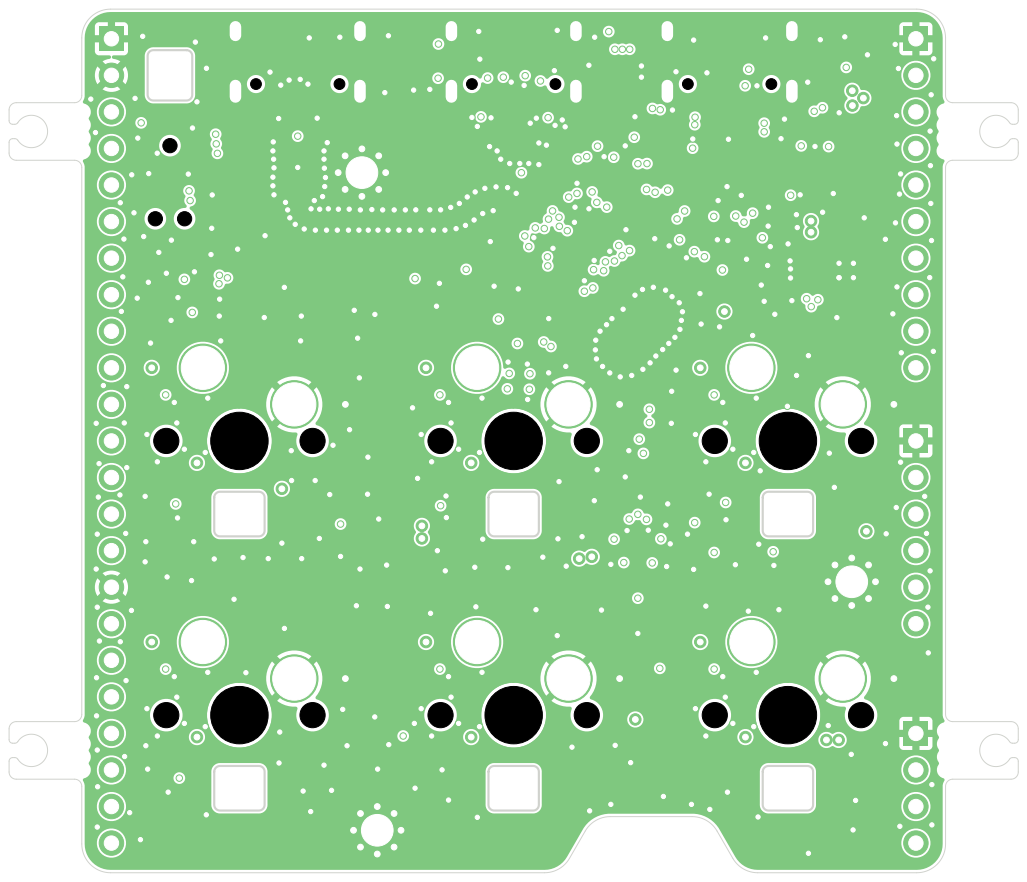
[picture p14: page 2]

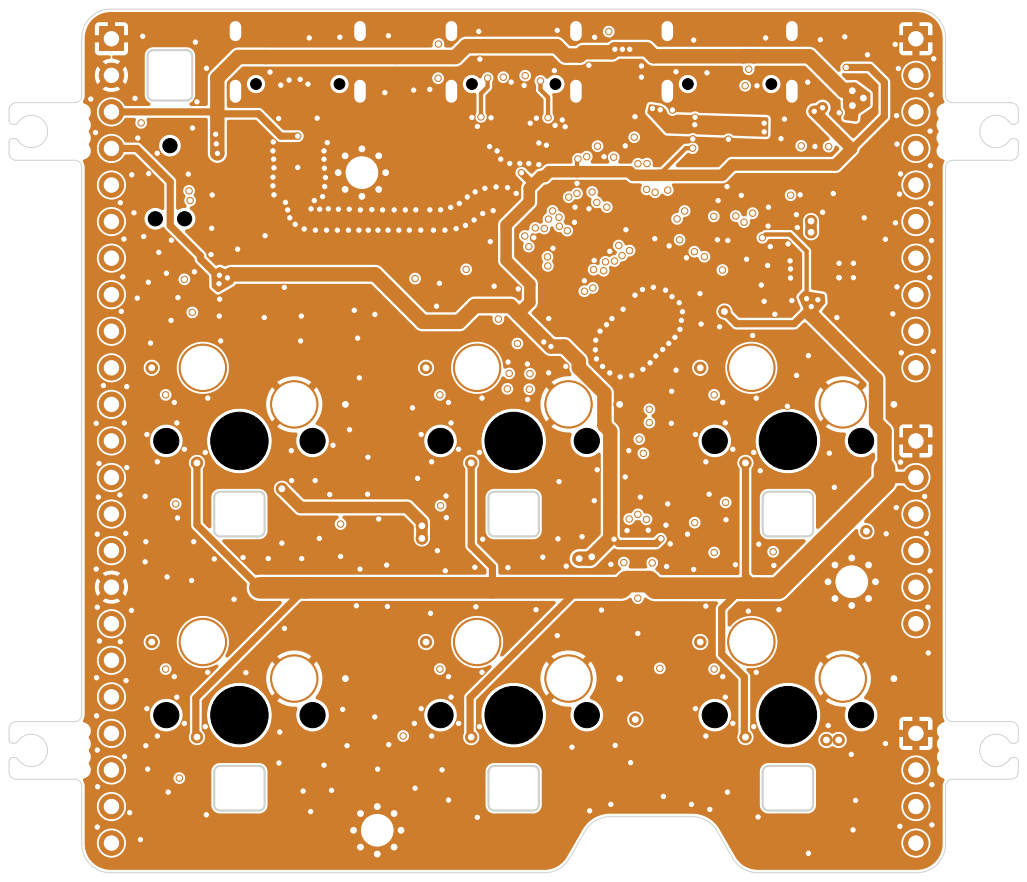
[picture p15: page 3]

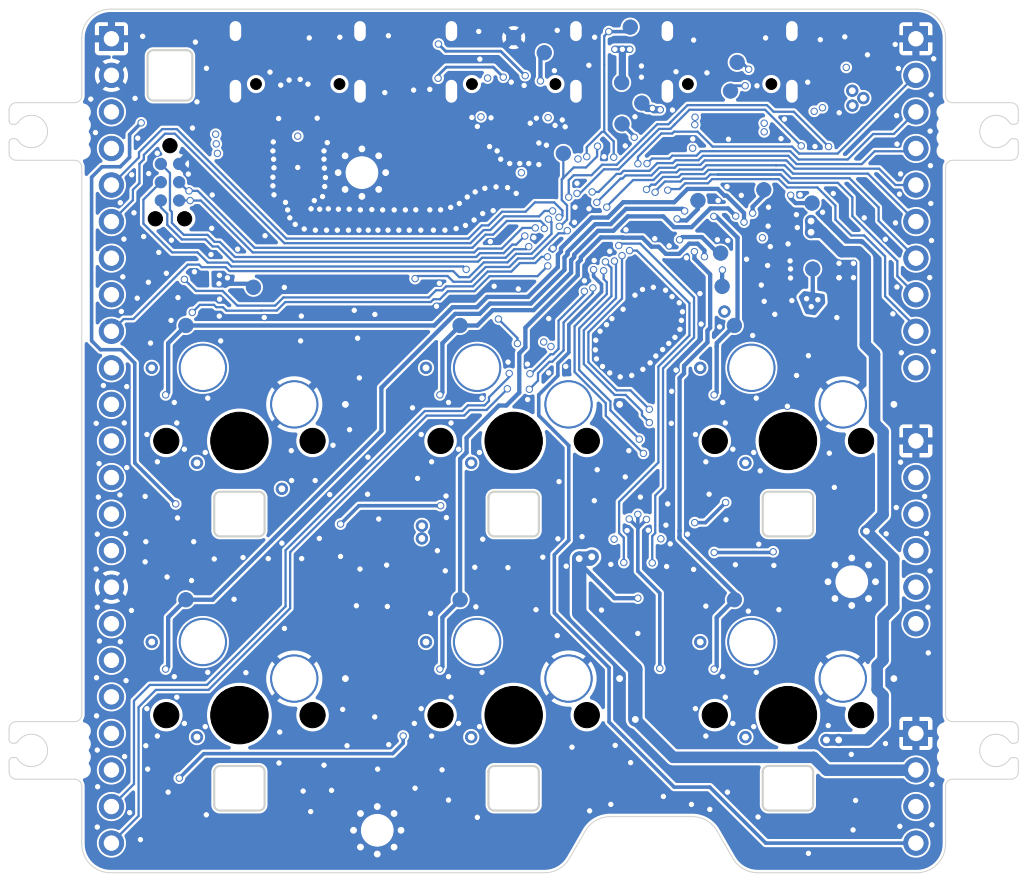
[picture p16: page 4]

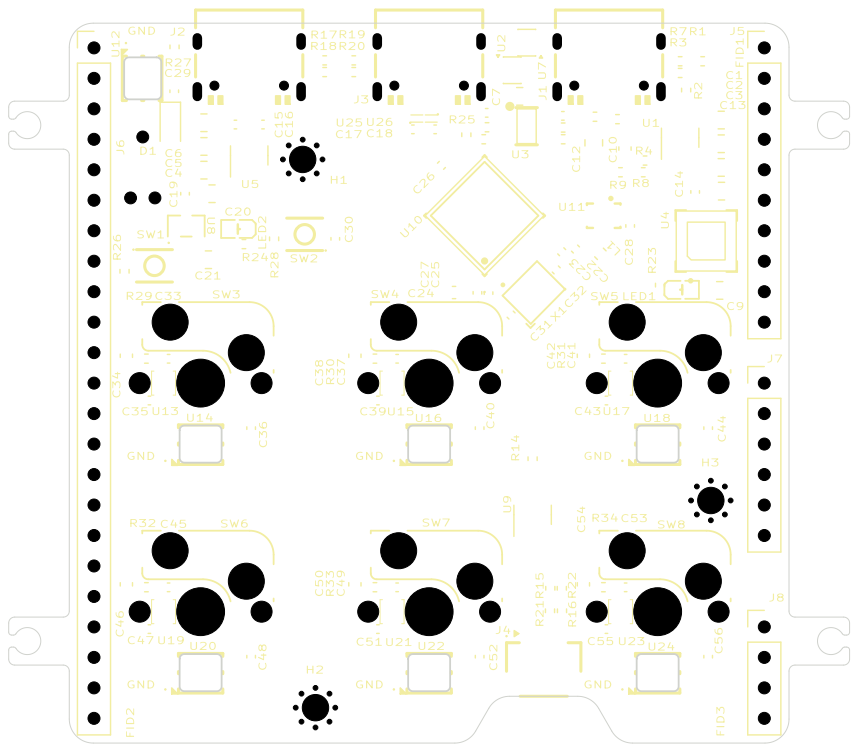
[picture p17: page 5]

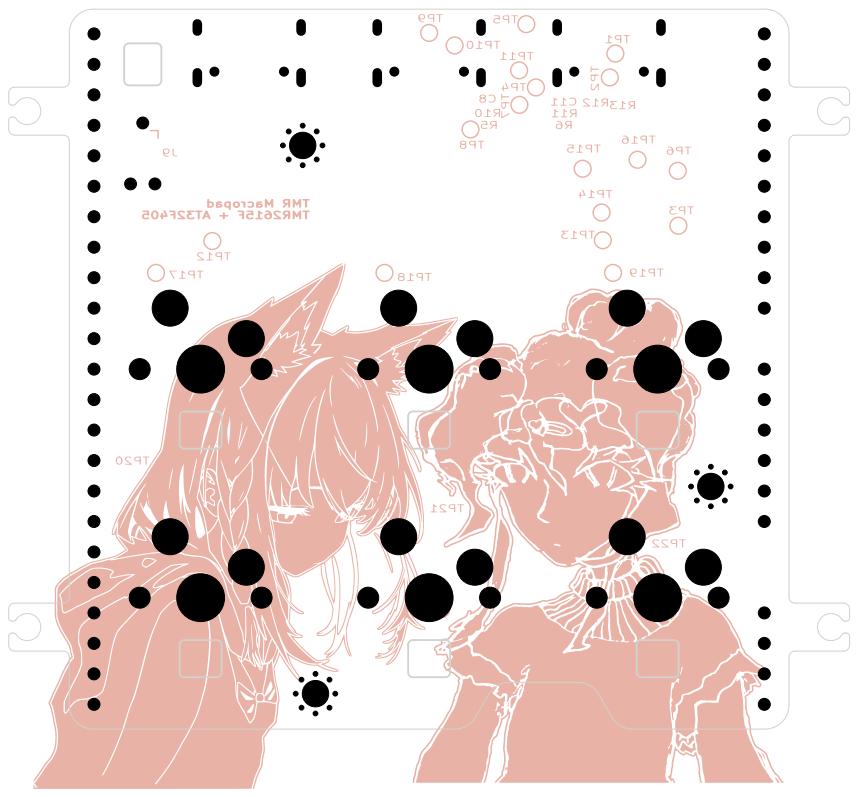
[picture p18: page 6]

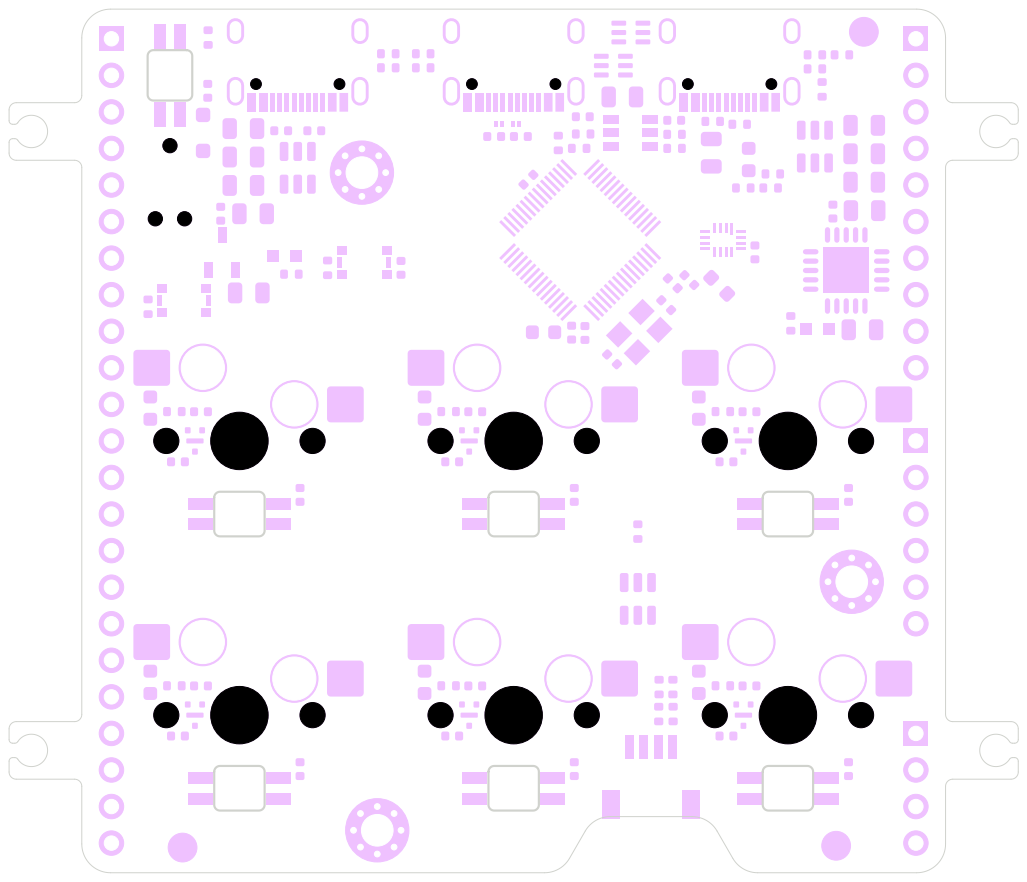
[picture p19: page 7]

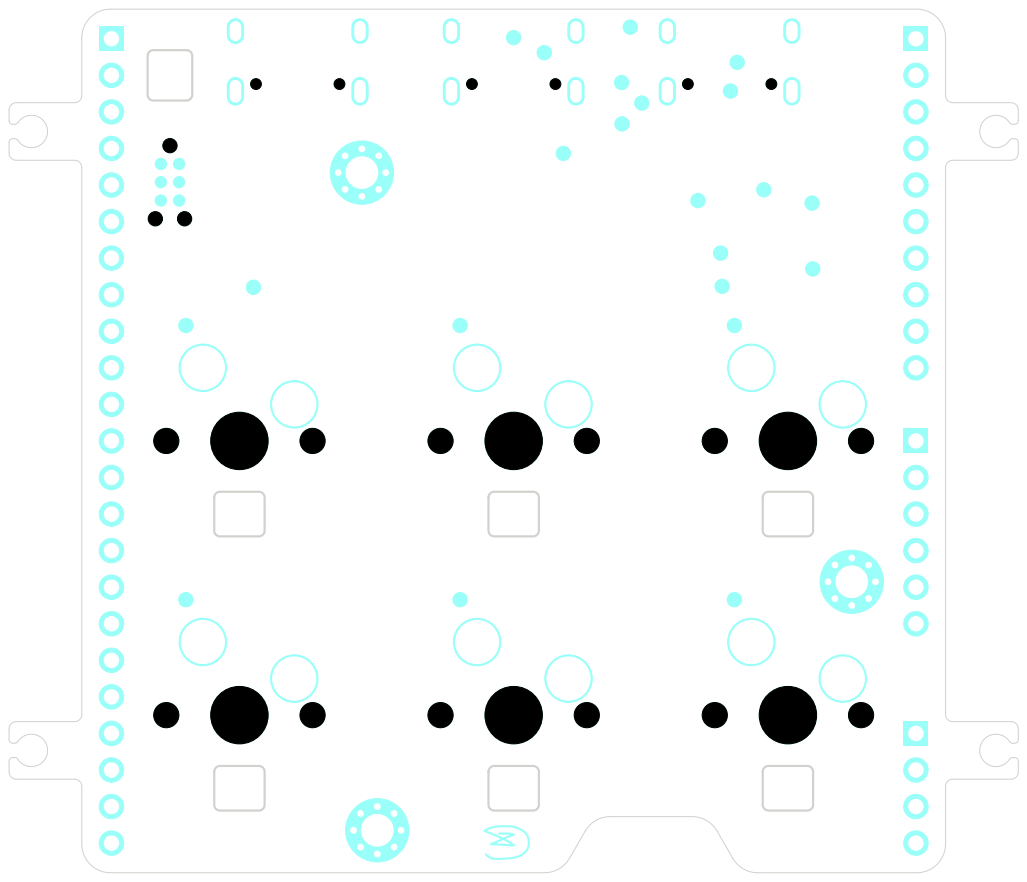
[picture p20: page 8]

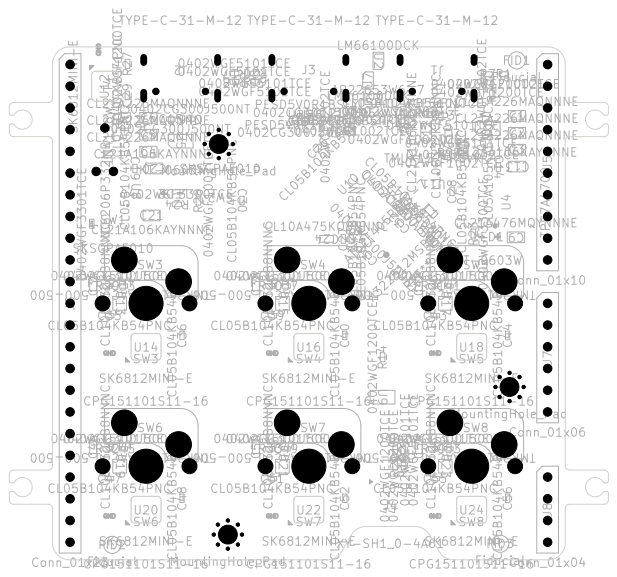
[picture p21: page 9]
