dubnubdubnub/Giris/hw/refs/switches/Gateron_MagneticJadeDelta_Dark-KS-20JDW10B055NW-G60.pdf

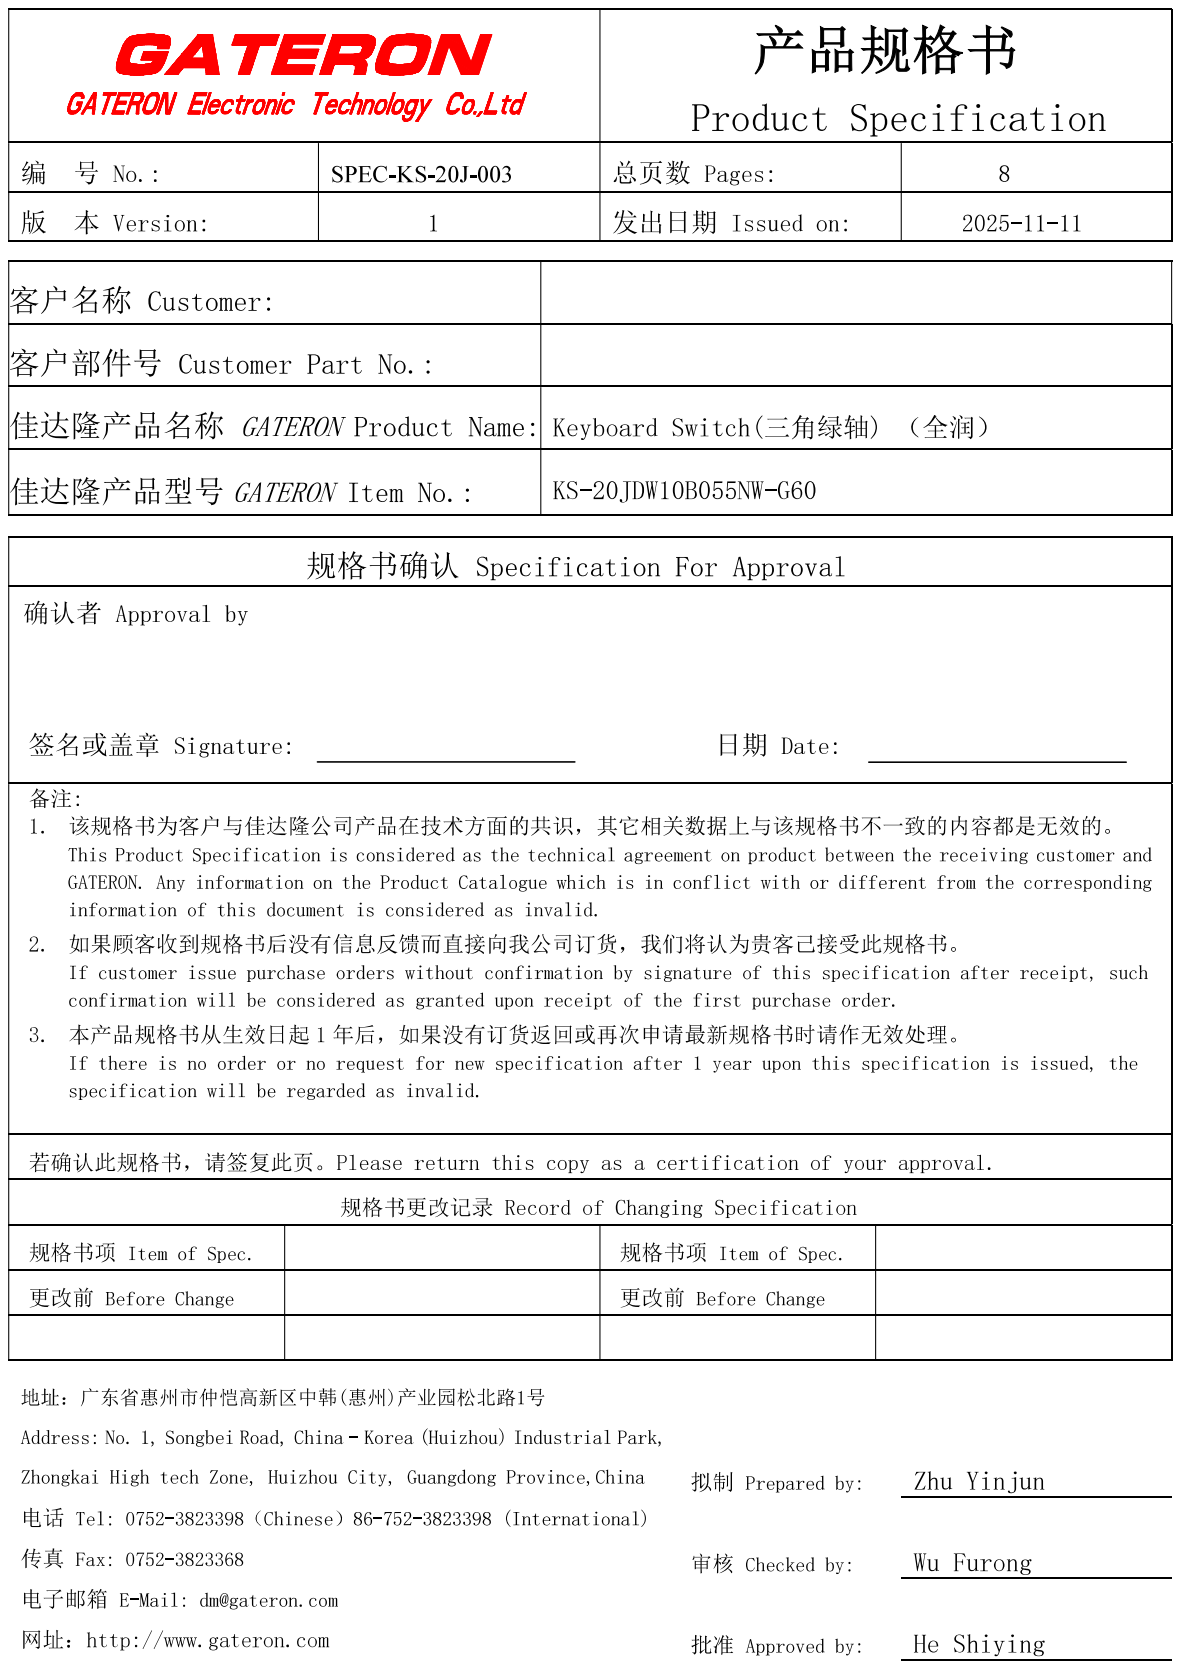
[picture p22: page 1]

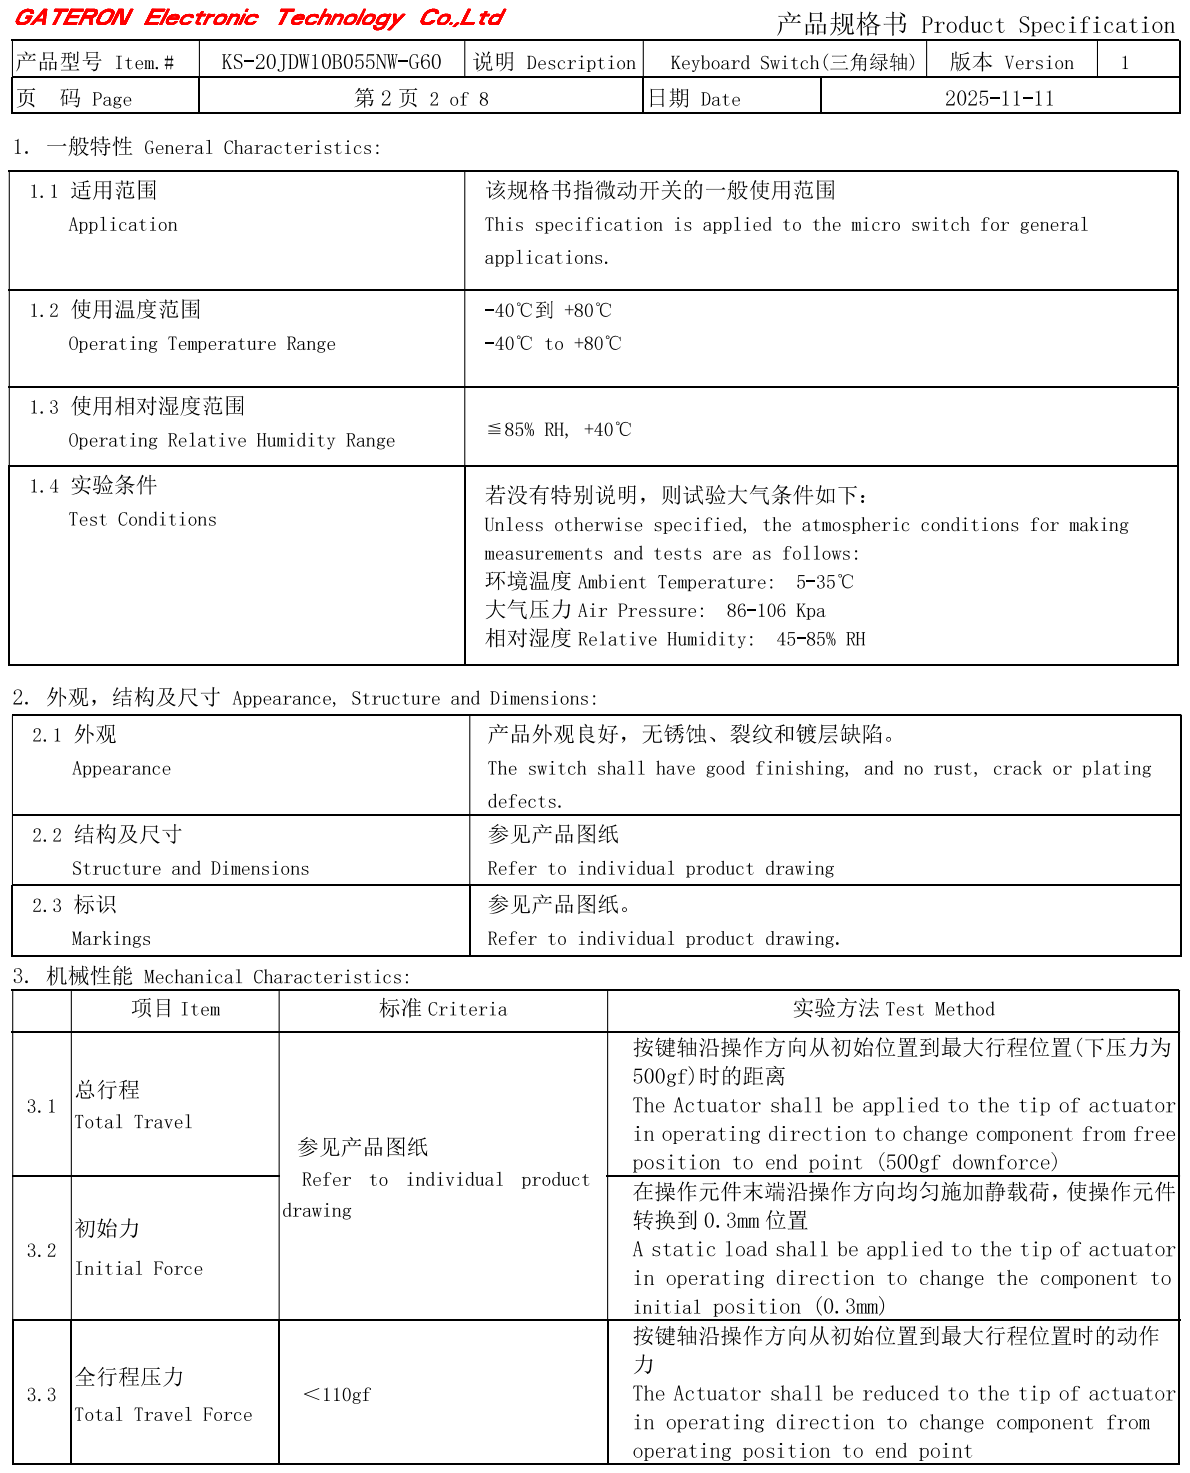
[picture p23: page 2]

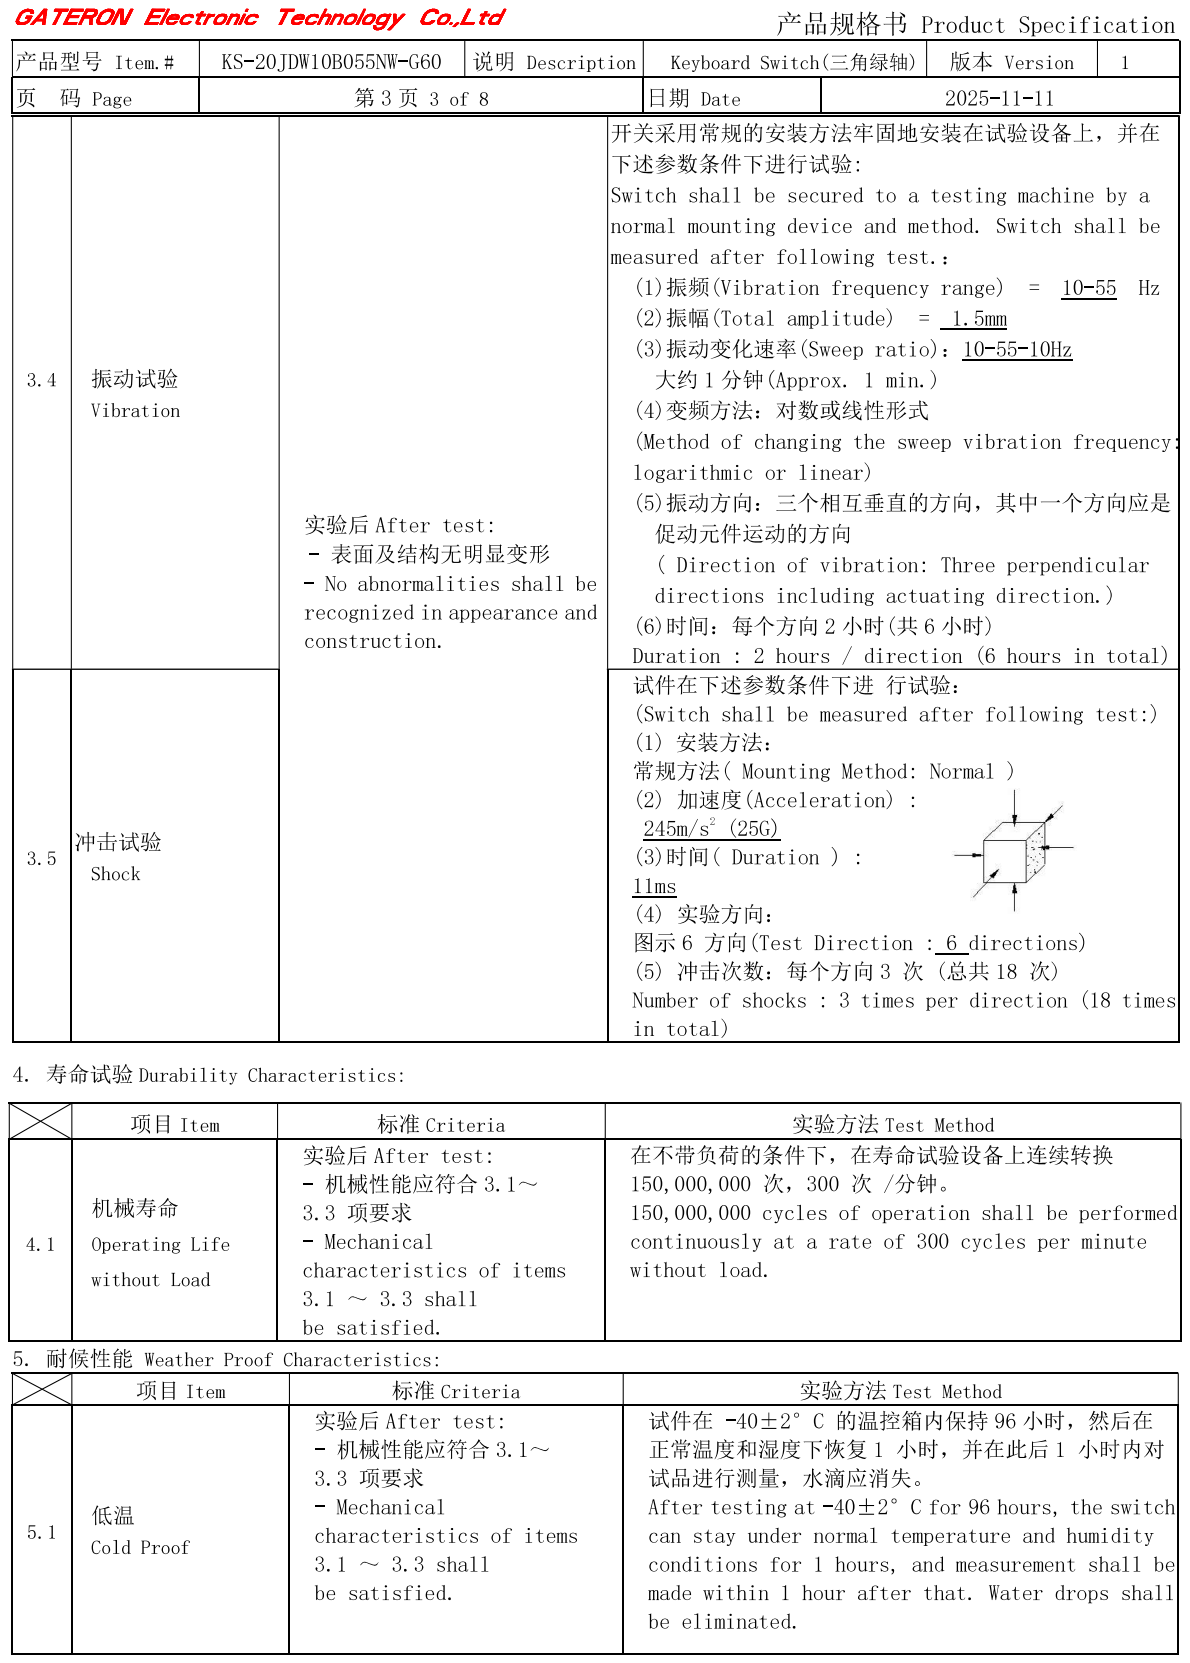
[picture p24: page 3]

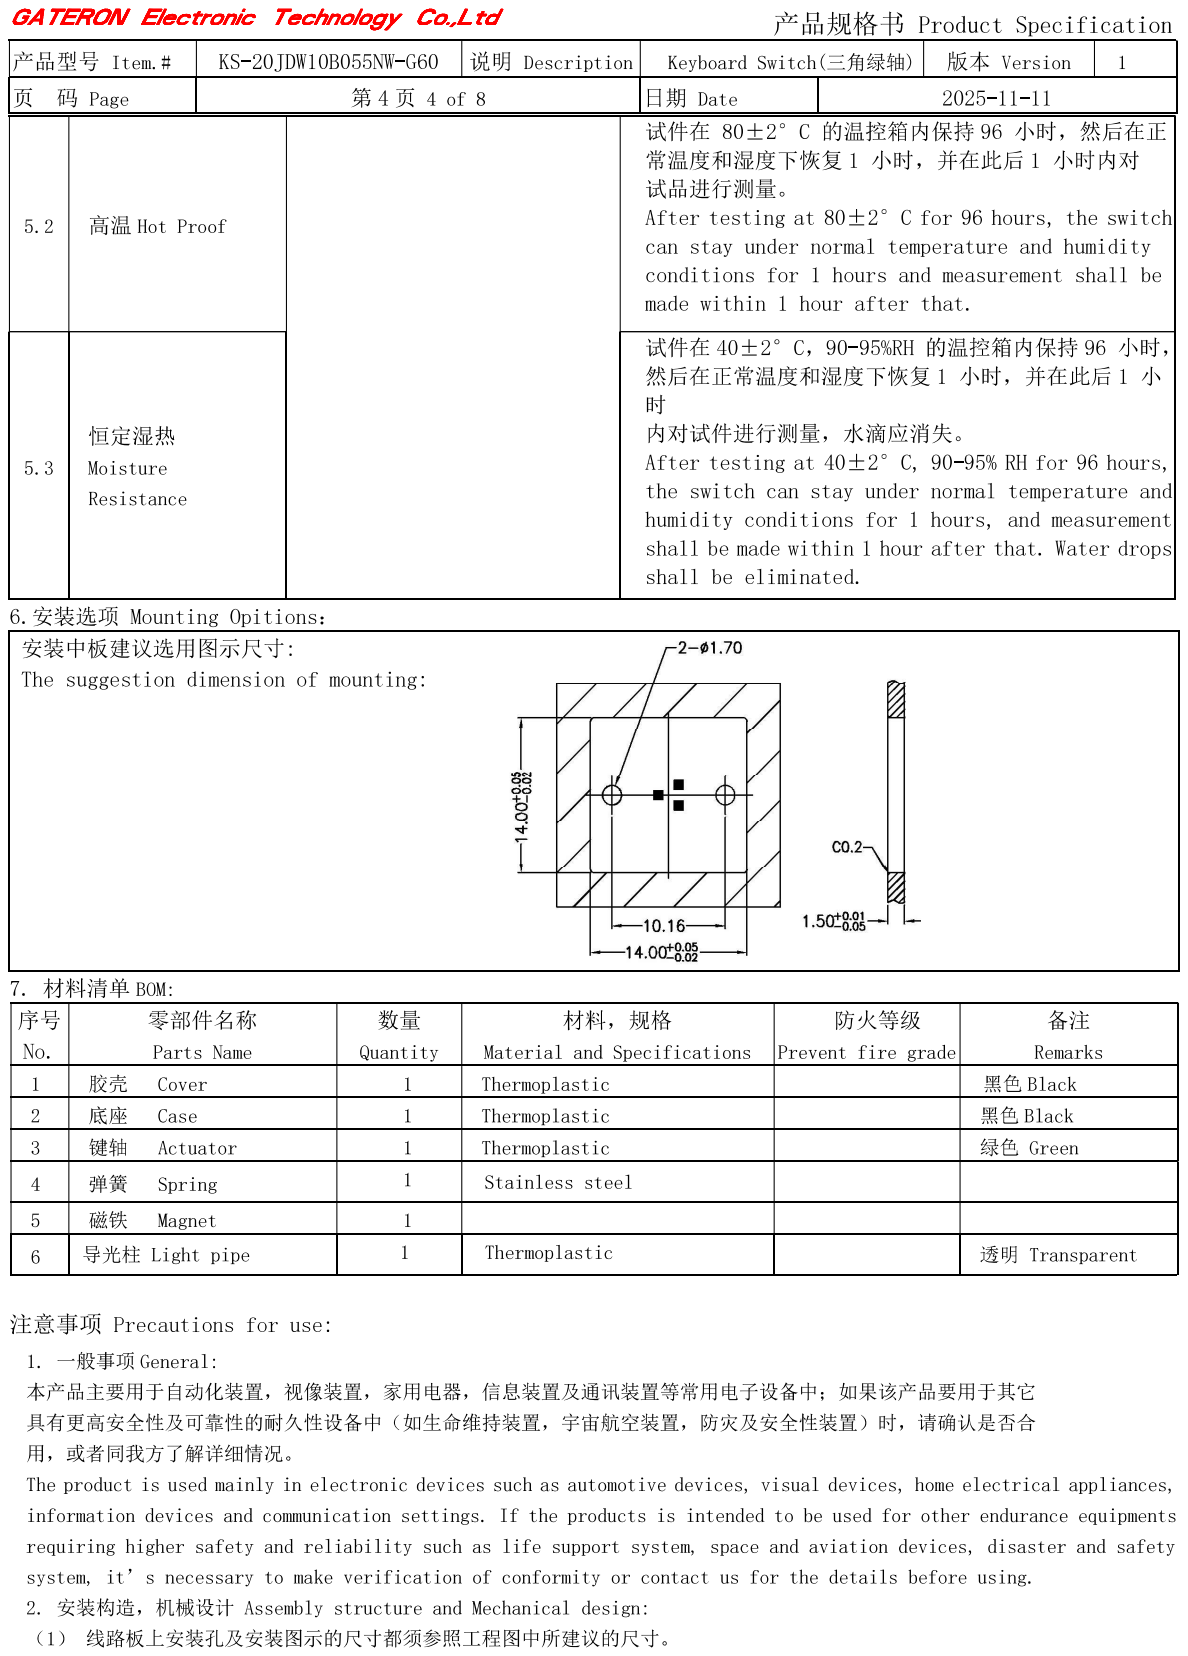
[picture p25: page 4]

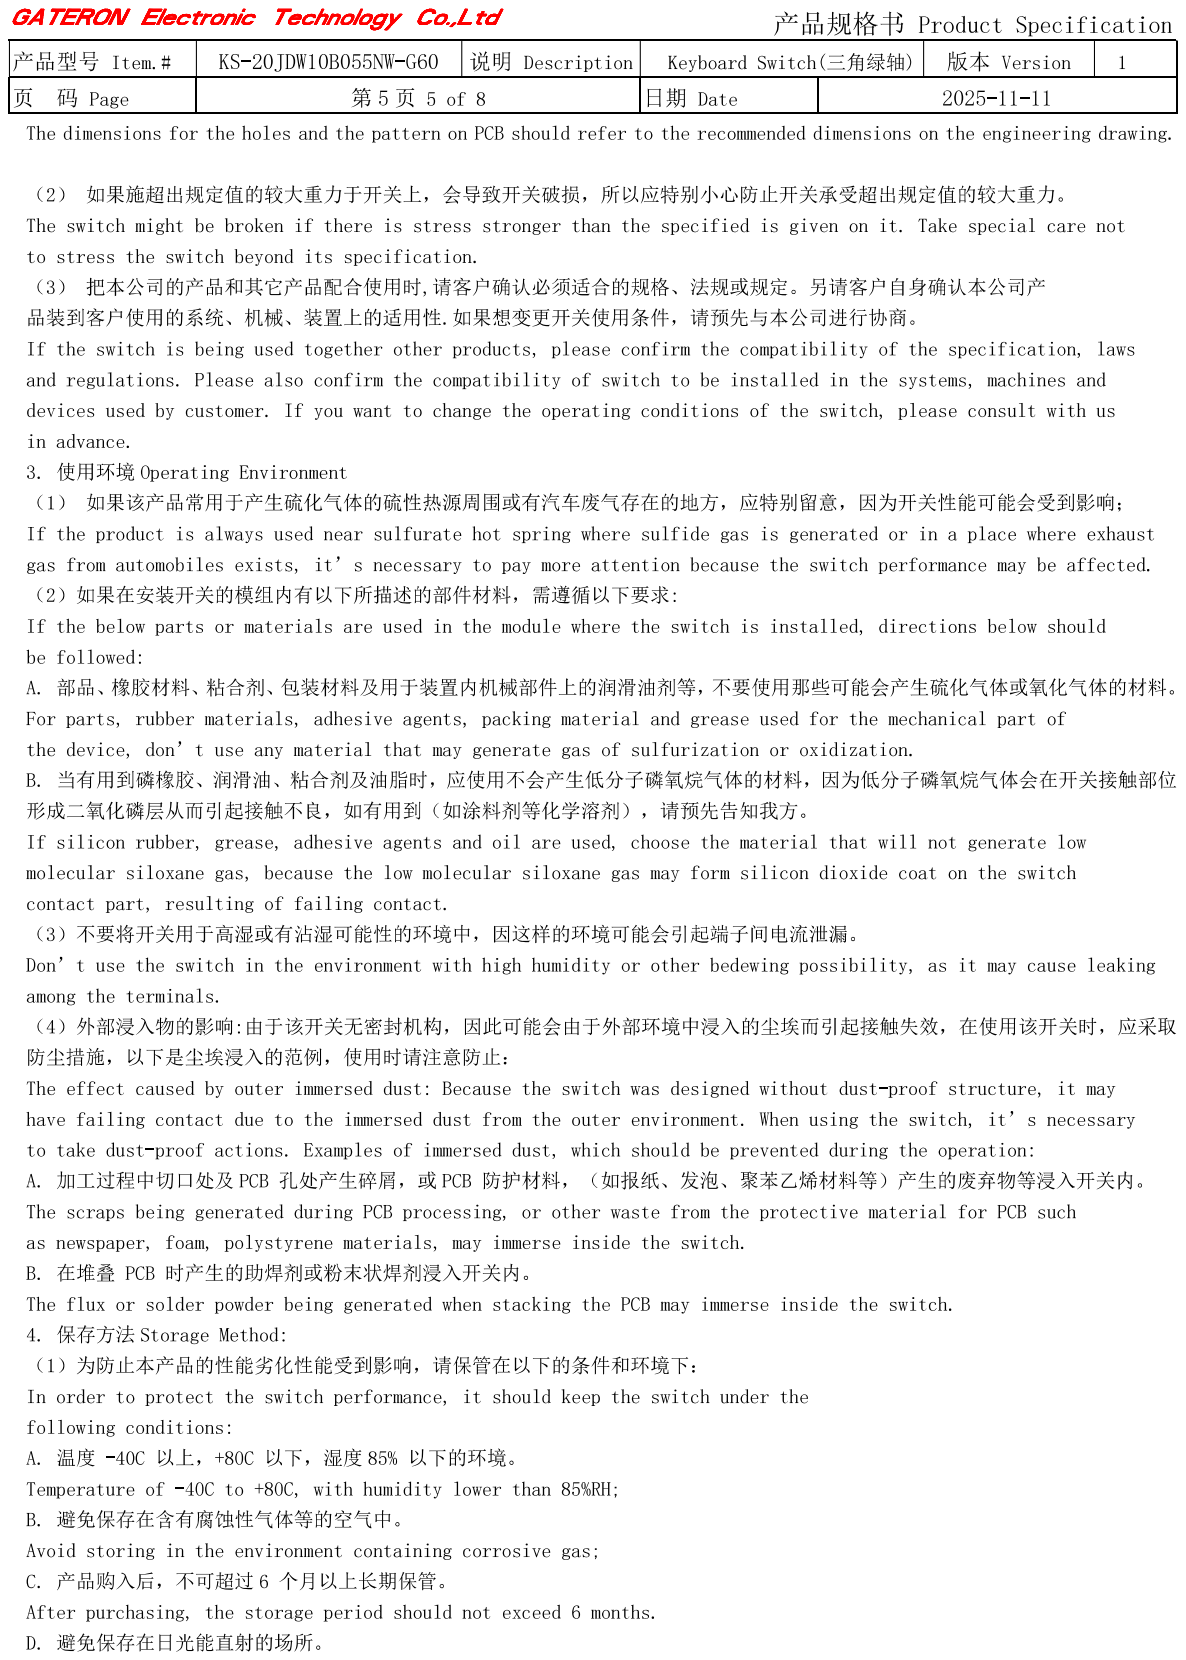
[picture p26: page 5]

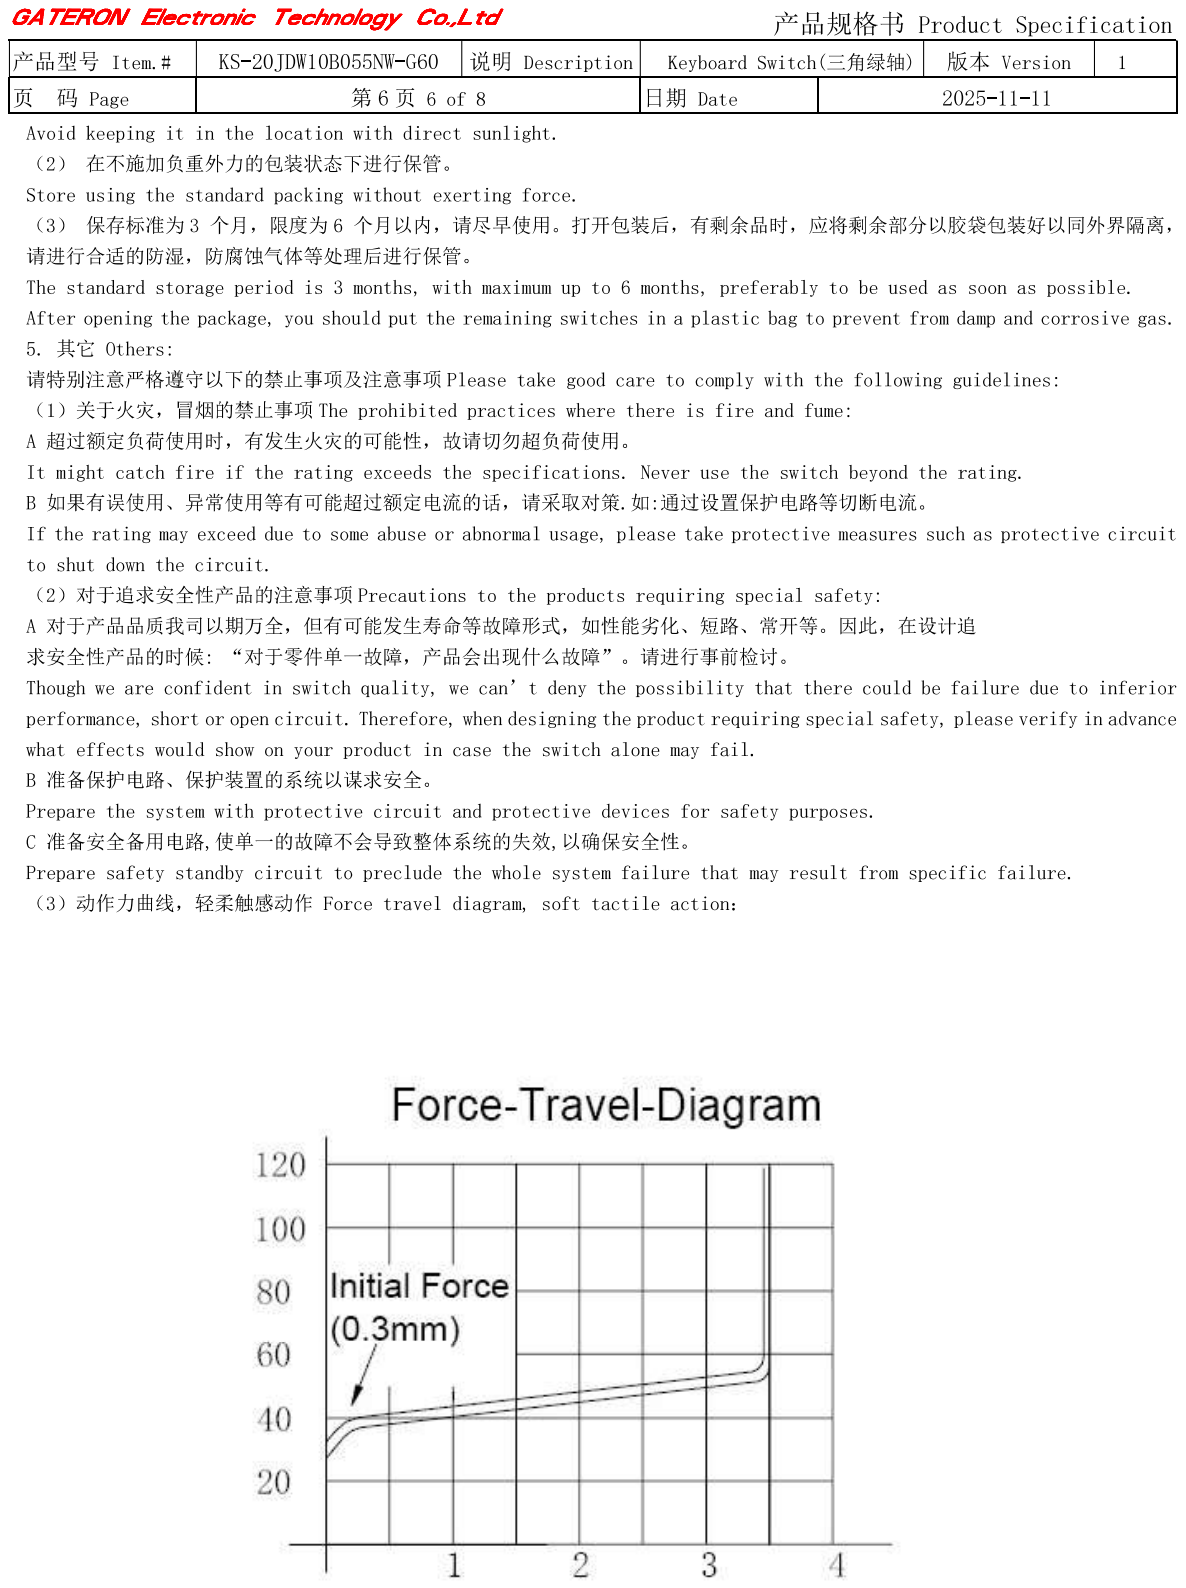
[picture p27: page 6]

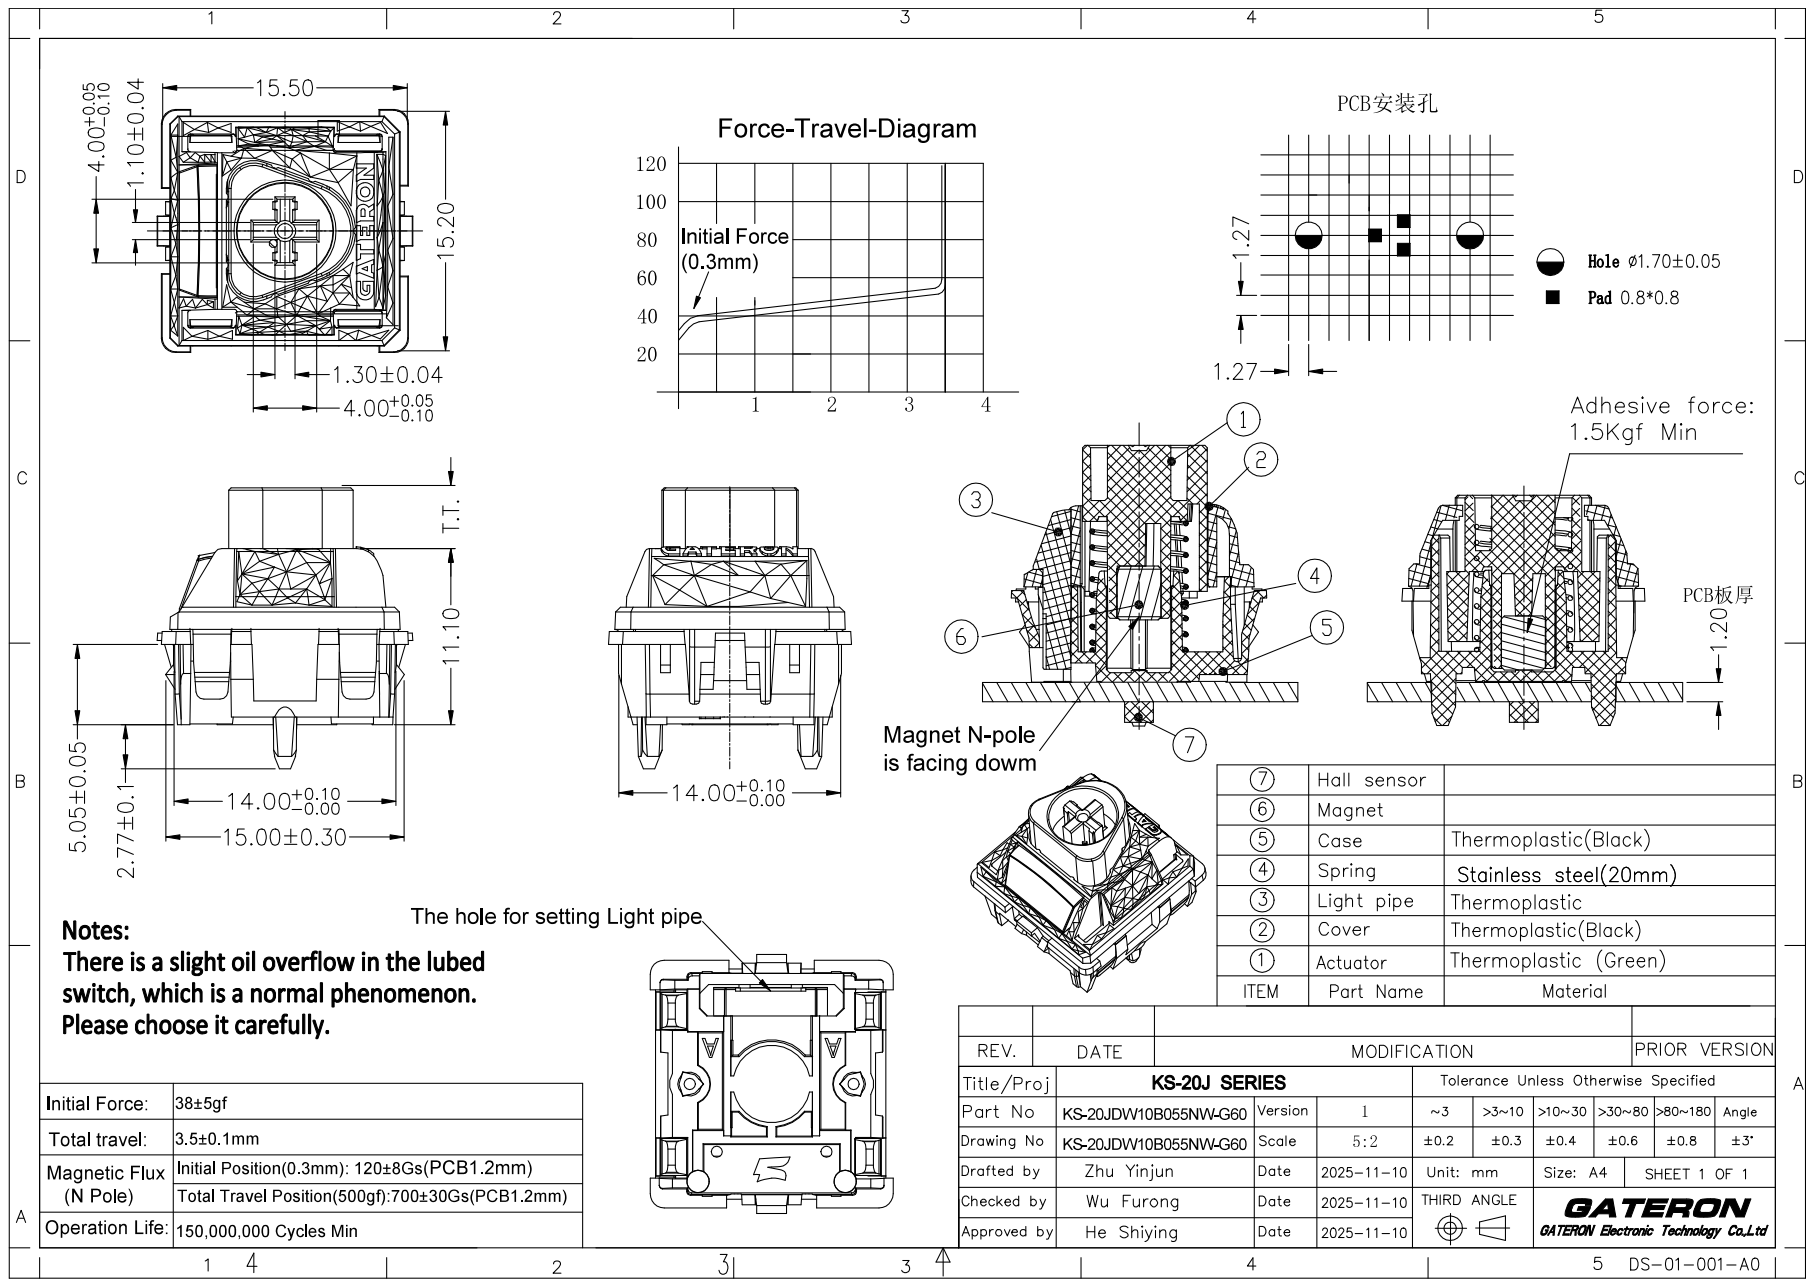
[picture p28: page 7]

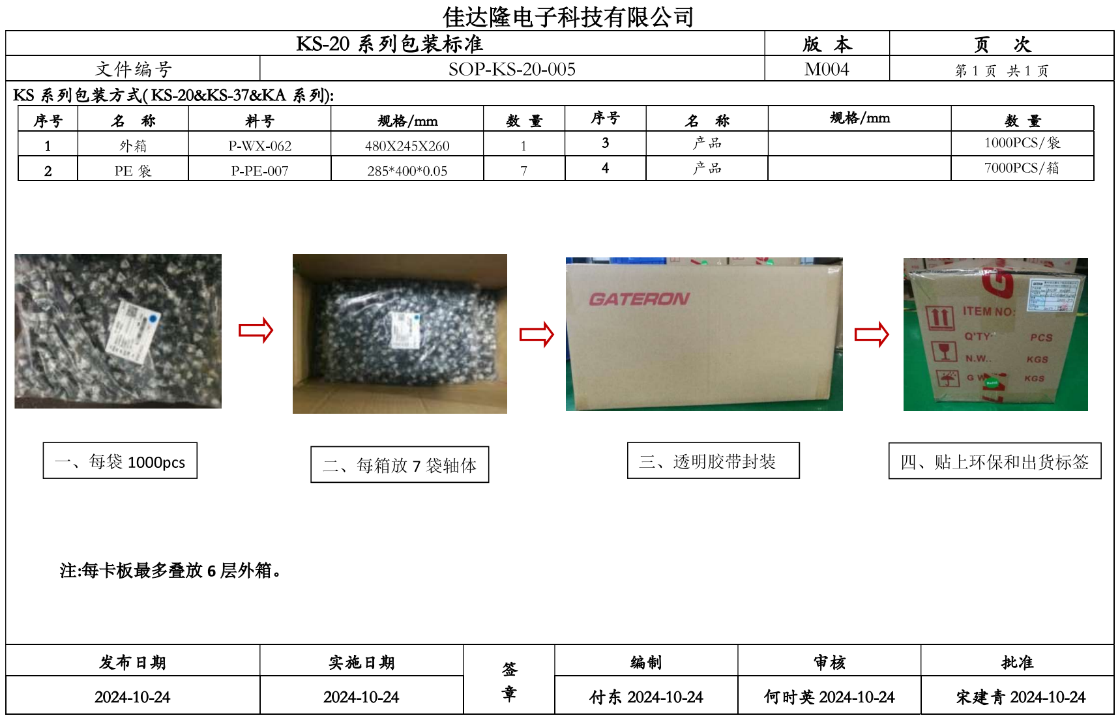
[picture p29: page 8]
